martinanus/salt/documentacion/Informe de tesis/src/3 - Diseño e implementación/3.2.9 - Tarjeta SD.tex

\subsubsection{Zócalo para memoria SD}

Para incluir una memoria SD en el sistema, se utilizó un zócalo modelo DM3AT-SF-PEJM5 de Hirose Connector \cite{DM3AT-SF-PEJM5}. Este conector admite memorias micro SD y tiene un sistema de \textit{push-pull} que permite manipular más fácilmente la colocación de la memoria. Para la memoria micro SD se utilizó el modelo Micro SD Ultra 8GB Clase 10 de Sandisk \cite{sd_sandisk} porque se reutilizó de otro proyecto. Sin embargo, al ser un componente de simple extracción y reemplazo, se considera que se debe utilizar una unidad de almacenamiento de mayor memoria. \\

En la figura \ref{fig:sd_sch} se observa la conexión del circuito con el zócalo para micro SD. Se utilizó la interfaz SPI del MCU para la comunicación con la SD y se colocaron algunas resistencias de \textit{pull-up} recomendadas en los buses de datos o líneas desconectadas. También se incluyeron capacitores de desacople para reducir el ruido en la alimentación de la SD. El zócalo incluye además una conexión mecánica que permite determinar si existe una memoria colocada en el zócalo o no; esto se conecta con una entrada del MCU para poder considerar el estado físico real de la memoria. 

\begin{figure}[H]
    \centering
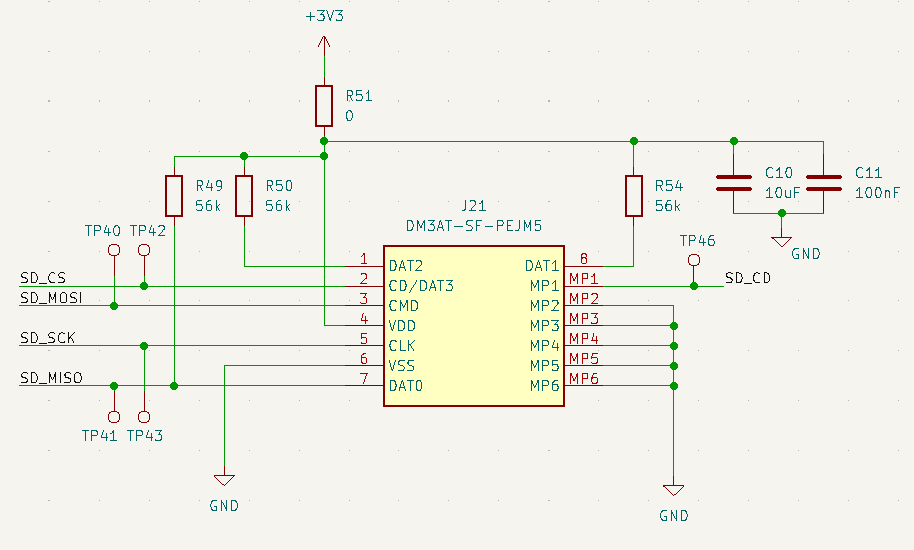
[picture p28: documentacion/Informe de tesis/src/img/sd_sch.png]
    
    \caption{Circuito de conexión del zócalo para memoria SD}
    \label{fig:sd_sch}
\end{figure}
