martinanus/salt/documentacion/Plan de Trabajo/src/7-Entregables.tex

\section{Entregables}

Se presenta a continuación una lista de los entregables del proyecto:

\begin{itemize}
    \item Documento de diseño de circuitos y selección de componentes
    \item Diseño de esquemático y layout de los PCB
    \item Desarrollo de firmware
    \item Prototipo funcional
    \item Documento de pruebas sobre el prototipo
    \item Informe integral del proyecto

    \end{itemize}
