martinanus/salt/documentacion/Informe de tesis/src/2 - Introducción específica/2.0 - intro.tex

En este capítulo se presentan los conceptos fundamentales necesarios para comprender el trabajo realizado, así como los módulos de hardware clave utilizados durante el desarrollo del sistema.
