martinanus/salt/documentacion/Informe de tesis/src/2 - Introducción específica/2.1 - intro.tex

\subsection{Módulos y componentes}

La figura \ref{fig:diagrama_bloques} muestra un diagrama en bloques del sistema, el cual proporciona una visión general que facilita la comprensión de los conceptos y módulos introducidos a lo largo de este capítulo.

\begin{figure}[H]
    \centering
    
    \caption{Diagrama en bloques del SAL/T}
    \label{fig:diagrama_bloques}
\end{figure}
