martinanus/salt/documentacion/Informe de tesis/src/1 - Introducción general/1.0 - intro.tex

En este capítulo se presenta el contexto, la motivación, los objetivos, el alcance y una descripción conceptual del proyecto. También se exponen sus requerimientos y una breve introducción a los sistemas críticos.
