martinanus/salt/documentacion/Informe de tesis/src/3 - Diseño e implementación/3.0 - intro.tex

En este capítulo se realiza una descripción general de la solución y se detalla el proceso de diseño e implementación del sistema a nivel hardware y firmware.
