martinanus/salt/documentacion/Informe de tesis/src/5 - Conclusiones/5.0 - intro.tex

En este capítulo se presentan las conclusiones generales obtenidas a partir de la realización del proyecto y los próximos pasos a seguir para la implementación del sistema en formaciones ferroviarias operativas.
