martinanus/salt/documentacion/Plan de Trabajo/src/8-DesgloseDeTareas.tex

\section{Desglose de Tareas}

Para realizar una mejor estimación de la duración del proyecto, es necesario descomponer el proyecto en tareas generales y estas en subtareas.  A continuación, se muestra un listado de todas las tareas necesarias para completar el proyecto con sus duraciones estimadas. 

\begin{enumerate}
    \item Estudio de Factibilidad   (60hs)
    \begin{enumerate}
        \item Lectura de documentos existentes sobre el SAL/T   (20hs)
        \item Lectura pliego de especificaciones técnicas SAL/T (5hs)
        \item Análisis y acuerdo de nuevas funcionalidad a implementar  (25hs)
        \item Entendimiento de código y puesta en marcha de primer prototipo SAL/T  (10hs)
    \end{enumerate}
    \item Diseño general de la solución (45hs)
    \begin{enumerate}
        \item Redacción de requerimientos del proyecto (7hs)
        \item Diseño de bloques de la solución (15hs)
        \item Análisis de comunicaciones entre módulos integrados (8hs)
        \item Análisis de disponibilidad de tiendas para componentes (10hs)
        \item Análisis de fabricantes de PCB (5hs)
    \end{enumerate}
    \item Desarrollo de hardware (255hs)
    \begin{enumerate}
        \item Investigación y selección de microcontrolador y kit de desarrollo (25hs)
        \item Investigación y selección de módulos GPS (10hs)
        \item Investigación y selección de módulos Wifi (10hs)
        \item Diseño de circuito de medición estado SIS (20hs)
        \item Diseño de circuitos RS485 (10hs)
        \item Diseño de panel frontal (15hs)
        \item Diseño circuitos de relé (15hs)
        \item Selección de componentes (40hs)
        \item Armado de esquemáticos (35hs)
        \item Asignación de pines microcontrolador (15hs)
        \item Selección de tecnología de PCB a utilizar (10hs)
        \item Diseño del PCB (50hs)
    \end{enumerate}
    \item Desarrollo de firmware (215hs)
    \begin{enumerate}
        \item Desarrollo conexión Wifi (15hs)
        \item Desarrollo de comunicación con protocolo MQTT (25hs)
        \item Desarrollo comunicación GPS (15hs)
        \item Desarrollo lecturas de velocidad (20hs)
        \item Desarrollo lectura de estados SIS (15hs)
        \item Desarrollo de lógica de perfiles intermitentes (15hs)
        \item Desarrollo de registro de datos local (25hs)
        \item Desarrollo de descarga de reporte de datos (25hs)
        \item Desarrollo de lógica general del sistema (30hs)
        \item Implementación de módulos en sistema operativo de tiempo real (30hs)
    \end{enumerate}
    \item Fabricación del prototipo (55hs)
    \begin{enumerate}
        \item Compra de componentes (10hs)
        \item Ensamblaje de componentes (15hs)
        \item Verificación de continuidad y señales en la placa (10hs)
        \item Pruebas sobre las comunicaciones (20hs)
    \end{enumerate}
    \item Verificación y validación (80hs)
    \begin{enumerate}
        \item Verificación de casos de uso del prototipo (35hs)
        \item Pruebas de integración (30hs)
        \item Validación de los requerimientos (20hs)
    \end{enumerate}
    \item Revisión de documentación (67hs)
    \begin{enumerate}
        \item Planificación del proyecto (15hs)
        \item Redacción del plan de trabajo (12hs)
        \item Documentación técnica del hardware (20hs)
        \item Documentación del código fuente (20hs)
        
    \end{enumerate}
    \item Presentación del proyecto (110hs)
    \begin{enumerate}
        \item Elaboración de diapositivas para la presentación (20hs)
        \item Confección del informe final (90hs)
    \end{enumerate}
\end{enumerate}

En total, se estiman 887 horas de trabajo necesarias para el desarrollo del proyecto. \\

Además, se presenta a modo de referencia, un cronograma con los plazos aproximados para completar cada una de las tareas generales. 

\begin{table}[h]
\begin{center}
\begin{tabular}{|l|l|l|l|l|l|l|l|l|l|l|l|l|}
\hline
\multicolumn{1}{|c|}{} & \multicolumn{12}{c|}{Meses} \\ \cline{2-13} 
\multicolumn{1}{|c|}
    {\multirow{-2}{*}{Tareas}} 
    & 1 & 2 & 3 & 4 & 5 & 6 & 7 & 8 & 9 & 10 & 11 & 12 \\ \hline
Estudio de Factibilidad             &
\cellcolor[HTML]{656565}{\color[HTML]{333333}}  &
                                                &
                                                &
                                                &
                                                &
                                                &
                                                &
                                                &
                                                &
                                                & 
                                                & \\ \hline
Diseño general de la solución                &
                                                &
\cellcolor[HTML]{656565}{\color[HTML]{333333}}  &                      
\cellcolor[HTML]{656565}{\color[HTML]{333333}}  &
                                                &
                                                &
                                                &
                                                &
                                                &
                                                &
                                                &
                                                & \\ \hline
Desarrollo de hardware      &
                                                &
                                                &    
\cellcolor[HTML]{656565}{\color[HTML]{333333}}  &
\cellcolor[HTML]{656565}{\color[HTML]{333333}}  &
\cellcolor[HTML]{656565}{\color[HTML]{333333}}  &
\cellcolor[HTML]{656565}{\color[HTML]{333333}}  &
                                                &
                                                &
                                                &
                                                &
                                                & \\ \hline
Desarrollo de firmware               &
                                                &
                                                &
                                                &
                                                &
                                                &
\cellcolor[HTML]{656565}{\color[HTML]{333333}}  &
\cellcolor[HTML]{656565}{\color[HTML]{333333}}  &
\cellcolor[HTML]{656565}{\color[HTML]{333333}}  &
                                                &
                                                &
                                                & \\ \hline
Fabricación del prototipo                                 &
                                                &
                                                &    
                                                &
                                                &
                                                &
                                                &
                                                &
                                                &
\cellcolor[HTML]{656565}{\color[HTML]{333333}}  &
                                                &
                                                & \\ \hline
Verificación y validación                &
                                                &
                                                &    
                                                &
                                                &
                                                &
                                                &
                                                &
                                                &   
\cellcolor[HTML]{656565}{\color[HTML]{333333}}  &
\cellcolor[HTML]{656565}{\color[HTML]{333333}}  &
                                                & \\ \hline
Revisión de documentación                &
                                                &                          
                                                &
                                                &
                                                &
                                                &
                                                &
                                                &
                                                &
                                                &            
\cellcolor[HTML]{656565}{\color[HTML]{333333}}  &
\cellcolor[HTML]{656565}{\color[HTML]{333333}}  & \\ \hline                                                
Presentación del proyecto                       &
                                                &
                                                &                          
                                                &
                                                &
                                                &
                                                &
                                                &
                                                &
                                                &
\cellcolor[HTML]{656565}{\color[HTML]{333333}}  &
\cellcolor[HTML]{656565}{\color[HTML]{333333}}  &
\cellcolor[HTML]{656565}{\color[HTML]{333333}}  \\ \hline
\end{tabular}
\end{center}
\end{table}
