martinanus/salt/documentacion/Informe de tesis/src/img/logo_fiuba_new.pdf

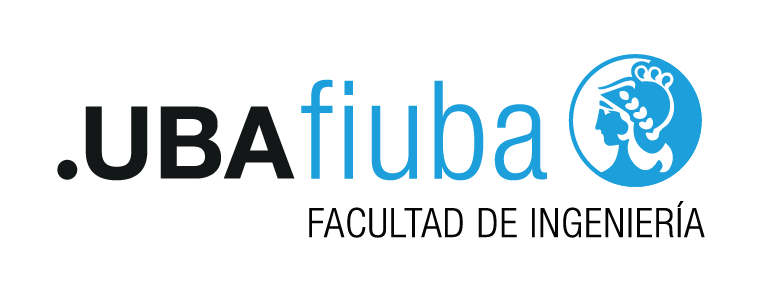
[picture p44: page 1]
