martinanus/salt/documentacion/Plan de Trabajo/Anus_SALT_Plan_de_trabajo.pdf

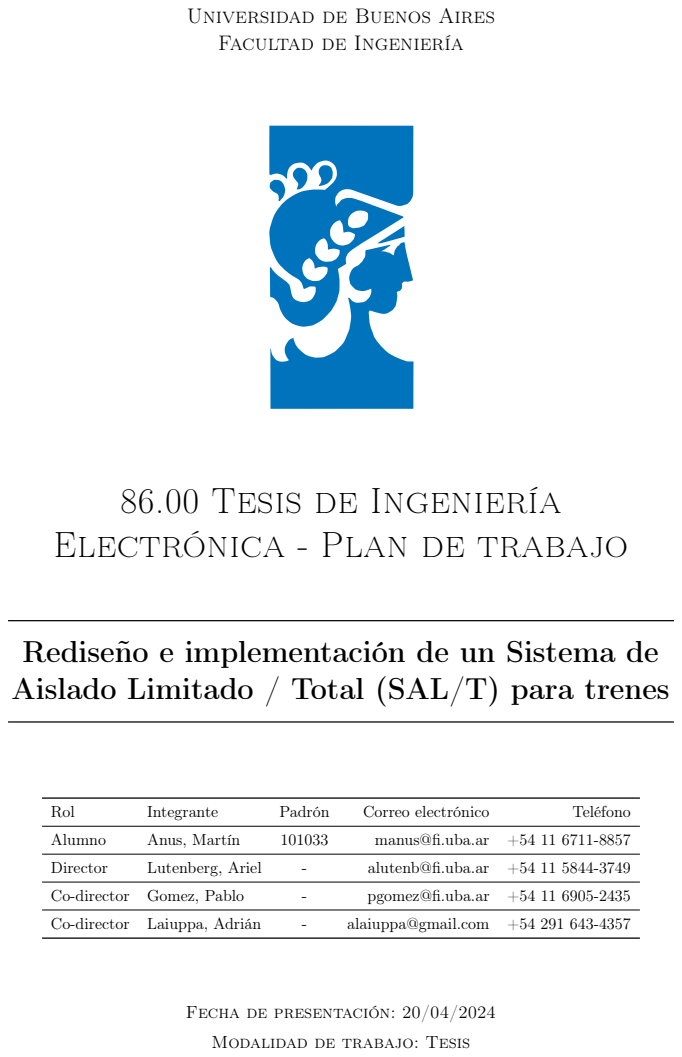
[picture p45: page 1]
Rol; Integrante; Padrón; Correo electrónico; Teléfono; Alumno; Anus, Martín; manus@fi.uba.ar +54 11 6711-8857; Director; Lutenberg, Ariel; alutenb@fi.uba.ar +54 11 5844-3749; Co-director Gomez, Pablo; pgomez@fi.uba.ar +54 11 6905-2435; Co-director Laiuppa, Adrián; alaiuppa@gmail.com +54 291 643-4357

Universidad de Buenos Aires

Facultad de Ingeniería

86.00 Tesis de Ingeniería

Electrónica - Plan de trabajo

Rediseño e implementación de un Sistema de
Aislado Limitado / Total (SAL/T) para trenes

Fecha de presentación: 20/04/2024

Modalidad de trabajo: Tesis

Sistema de Aislado Limitado / Total (SAL/T) | UBA - Facultad de Ingeniería

### Índice

1. Descripción | 1
2. Antecedentes | 2
3. Áreas profesionales de relevancia | 3
4. Objetivos | 4
5. Necesidad y soluciones existentes | 4
6. Alcance | 5
7. Entregables | 5
8. Desglose de Tareas | 6
9. Referencias | 8
10.Anexo | 9

### 1. Descripción

Las formaciones ferroviarias cuentan con varios Sistemas Instrumentados de Seguridad (SIS) a bordo con el objetivo de supervisar el correcto funcionamiento de los subsistemas críticos como por ejemplo, la protección de coche a la deriva, el sistema de hombre vivo o la seguridad de puertas.

Estos sistemas están diseñados para que, ante la detección de una falla crítica, se produzca la detención de la formación de manera inmediata. Esto se logra controlando las señales de Corte de Tracción (CT) y de Freno de Emergencia (FE). En esta situación, la formación puede ser remolcada o bien, desactivar todos los SIS bajo estricta supervisión y continuar andando con el control manual del conductor hasta una estación cercana para descender a los pasajeros y luego a un taller para ser reparada.

El Sistema de Aislamiento Limitado/Total, por sus siglas SAL/T, es un equipo que permite una circulación controlada y más segura de la formación cuando uno de los SIS se encuentra en falla. Al activar el Modo Aislado Limitado (MAL), el SAL/T va a deshabilitar solamente el SIS que está en fallo y controlar las señales de CT y FE para poder continuar con la circulación de la formación. Para hacerlo de manera segura, el SAL/T va a contar con múltiples fuentes de medición de la velocidad de la formación y va a activar las señales de CT y FE para frenarla en caso de que se excedan los límites estipulados. En el Modo Aislado Total (MAT), se libera la velocidad de precaución y puede ser solamente aplicado por personal superior en el caso que la formación se encuentre sin pasajeros y muy alejada del centro reparador. Ambas activaciones deben ser registradas dentro del equipo así como también cualquier falla detectada, cambio de configuración en las velocidades permitidas o cualquier evento significativo para la seguridad de la formación.

Además, el SAL/T cuenta con otras funcionalidad como la comunicación con el conductor a través de una interfaz donde se muestra el estado de los SIS, la velocidad medida en todo momento y un indicador de la zona donde se encuentra la formación. En caso de no contar con una medición de velocidad válida y activar el MAL, el SAL/T entra en Modo Intermitente (MI) y controla la formación activando y desactivando la tracción y el freno acorde a los perfiles de tiempos preconfigurados según las características de la formación para no exceder ciertas velocidades de precaución. Desde el panel formal, el conductor puede seleccionar distintos perfiles intermitentes. También, el SAL/T tiene la posibilidad de conectarse con una central operativa para informar su estado y recibir remotamente instrucciones.

Este equipo es considerado un sistema crítico ya que, en caso de fallar, puede conllevar pérdidas de vidas humanas o daños importantes tanto de propiedades como del entorno.

En el 2019, el Ingeniero Iván Di Vito presentó un prototipo de este sistema con pruebas de campo en los talleres de Trenes Argentinos siguiendo las fases y recomendaciones de la norma UNE-EN 50126 [1]; “Aplicaciones ferroviarias. Especificación y demostración de la fiabilidad, la disponibilidad, la mantenibilidad y la seguridad (RAMS)”. En el año 2022, los ingenieros Fernando Iglesias y Matías Sambrizzi realizaron el trabajo “Central Operativa para el SAL/T” donde se desarrolló la central operativa para monitorear, controlar y configurar múltiples formaciones equipadas con el SAL/T de manera remota desde un centro de operaciones. Ambos trabajos fueron desarrollados con el acompañamiento del Grupo de Investigación en Calidad y Seguridad de las Aplicaciones Ferroviarias (GICSAFe) como trabajo final de grado de Ingeniería Electrónica en la Universidad de Buenos Aires teniendo como directores al Dr. Ing. Ariel Lutenberg y al Dr. Ing. Pablo Gomez.

En este trabajo, se busca hacer un rediseño del prototipo del SAL/T implementando algunas mejoras sugeridas por Trenes Argentinos en el pliego de especificaciones técnicas ET.SO.No 046/18–E3 del 2022, utilizando un microcontrolador y componentes más modernos y un firmware basado en un sistema operativo de tiempo real que resulte más portable que el actual. A continuación se muestra un diagrama en bloques del sistema a desarrollar:


Figura 1: Diagrama en bloques del SAL/T

También se muestra la interfaz humano-máquina (IHM) diseñada para comunicarse con el conductor de la formación:

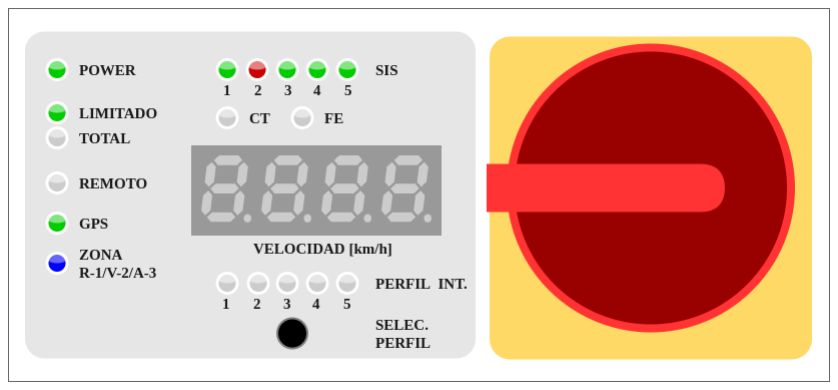
[picture p46: figure]

Figura 2: Interfaz humano-máquina del SAL/T

### 2. Antecedentes

El Grupo de Investigación en Calidad y Seguridad de las Aplicaciones Ferroviarias (GICSA-Fe) fue creado en 2017 en el marco del Consejo Nacional de Investigaciones Científicas y Técnicas (CONICET) de la República Argentina [2]. En el grupo participan investigadores, docentes y alumnos de diferentes instituciones públicas argentinas quienes realizan desarrollos de sistemas electrónicos e informáticas para aplicaciones ferroviarias relacionadas con la seguridad. Muchos de los prototipos desarrollados son instalados y entregados junto a toda la documentación, respetando normas internacionales de seguridad, para luego transferir el derecho de uso, fabricación y mantenimiento a los clientes.

La empresa estatal Trenes Argentinos Operaciones [3] encargó al grupo CONICET-GICSAFe el desarrollo de un prototipo del SAL/T en el año 2017. El ingeniero Iván Di Vito, en ese momento estudiante de la carrera de Ingeniería Electrónica en la UBA y allegado al grupo de investigación tomó el proyecto que finalizaría en el año 2019 con la entrega de un prototipo funcional del SAL/T luego de varias pruebas de campo en los talleres de Trenes Argentinos junto a toda la documentación requeridas por las normas de seguridad ferroviarias para este tipo de desarrollos [4]. El trabajo realizado incluyó el relevamiento de los requerimientos del proyecto, el desarrollo conceptual de la solución propuesta, el diseño e implementación del hardware y firmware, la puesta en marcha y realización de pruebas de campo de un prototipo funcional. El mismo se realizó de acuerdo a la norma UNE-EN 50126, aplicando técnicas de patrones de diseño de hardware y software [5]. Este trabajo fue publicado por el Congreso Argentino de Sistemas Embebidos (CASE) en el año 2019 en la categoría de artículo [6].

En el año 2021, otros dos estudiantes de la carrera de Ingeniería Electrónica de la UBA, Fernando Iglesias y Matias Sambrizzi, emprendieron un proyecto para el desarrollo de la central operativa del SAL/T en el mismo contexto de acuerdo entre Trenes y CONICET-GICSAFe. El objetivo de dicho proyecto fue desarrollar el software de una central operativa que permita administrar y configurar de forma remota dispositivos de supervisión de seguridad de formaciones ferroviarias SAL/T [7]. Para esto, se implementó un servicio de monitoreo y control que permite visualizar en tiempo real los datos recibidas y enviar comando de control a los dispositivos activos, la gestión de configuración de dispositivos, la base de datos, los componentes de seguridad necesarios para las comunicaciones e información almacenada y la gestión de usuarios y perfiles.

### 3. Áreas profesionales de relevancia

Esta Tesis está enmarcada principalmente dentro del área de Sistemas Digitales y Computación, según lo especificado en la versión 2009, Modificación 2018, del plan de estudios de la Carrera de Ingeniería Electrónica de la Facultad de Ingeniería de la Universidad de Buenos Aires [8].

En particular, están vinculadas a este proyecto las siguientes actividades reservadas al tıitulo de Ingeniero Electrónico:

- Diseñar, proyectar y calcular hardware y software de sistemas embebidos y dispositivos lógicos programables
- Proyectar, dirigir y controlar la construcción, implementación, mantenimiento y operación de lo mencionado anteriormente.

De la misma forma, son particularmente relevantes al proyecto los siguientes alcances del titulo de Ingeniero Electrónico:

- Estudio, planificación, proyectos, estudios de factibilidad técnico-económicos, programación, dirección, construcción, instalación, puesta en marcha, operación, ensayo, mediciones, mantenimiento, reparación, modificación, transformación e inspección de:

- Sistemas, subsistemas, equipos, componentes, partes, piezas (Hardware), de procesamiento electrónico de datos en todas sus aplicaciones incluyendo su programación (Software) asociada.
- Sistemas, subsistemas, equipos, componentes, partes, piezas que impliquen electrónica, de navegación o señalización o cualquier otra aplicación al movimiento de vehículos terrestres, aéreos, marítimos o de cualquier otro tipo.

### 4. Objetivos

### 4.1. Objetivos generales

Se busca diseñar una solución para aumentar la seguridad en las formaciones ferroviarias ante fallas en los Sistemas Instrumentados de Seguridad mediante un mejor control y monitoreo de velocidad de la formación en tiempo real. La solución debe ser compatible con los mecanismos de seguridad y sistemas instalados actualmente en las formaciones de Trenes Argentinos.

### 4.2. Objetivos particulares

- Rediseñar el sistema SAL/T a partir de los trabajos existentes y el pliego de especificaciones técnicas propuestos por Trenes Argentinos
- Rediseñar el hardware del SAL/T utilizando componentes vigentes en el mercado
- Generar un firmware portable basado en un sistema operativo de tiempo real
- Construir un prototipo del proyecto y realizar pruebas de funcionamiento en un entorno similar al real
- Favorecer el desarrollo de tecnología nacional

### 5. Necesidad y soluciones existentes

La empresa de Trenes Argentinos mencionó en reiteradas oportunidades la disconformidad con la situación actual de las formaciones ferroviarias frente a algún fallo en los Sistemas Instrumentados de Seguridad (SIS) ya que, al entrar alguno de ellos en fallo, obliga a la formación a ser remolcada o, lo que sucede más frecuentemente en la práctica, a continuar hasta la próxima estación para descender a los pasajeros deshabilitando todos los SIS con los que cuenta la formación. Esto presenta una situación de riesgo ya que la formación pasa a depender fuertemente de la manualidad del conductor sin ningún sistema de seguridad monitoreando y asistiendo la conducción.

Al mismo tiempo, la empresa no encuentra alternativas comerciales para satisfacer las necesidades de un Sistema de Aislamiento Limitado / Total ya que necesita integrar distintos SIS y fuentes de medición que no son necesariamente del mismo fabricante o con especificaciones genéricas que permitan su fácil integración.

Por estos motivos, Trenes Argentinos solicitó al grupo CONICET-GICSAFe que diseñara un SAL/T a medida para cumplir con los requerimientos específicos de sus formaciones. En 2019 se entregó una primera versión del prototipo que permitía satisfacer las funciones más importantes del sistema. Sin embargo, antes de requerir una versión productiva y fabricable en cantidades, se determinó que faltaban implementar algunas funcionalidades adicionales para que se pueda instalar un SAL/T en las formaciones. El pliego de especificaciones técnicas para la versión completa del SAL/T se encuentra en disponible en [9].

Los cambios más relevantes mencionados en el documento que dan lugar a rediseñar el prototipo antes de producirlo en masa son:

- Utilización de un microcontrolador de mayor capacidad y más vigente
- Generación de un firmware más portable basado en un sistema operativo de tiempo real
- Aislamiento del SIS en falla particular en Modo Aislado Limitado sin interrumpir el funcionamiento del resto de los SIS
- Selección de distintos perfiles intermitentes desde el panel frontal del SAL/T
- Conector de zona para poder determinas distintas zonas de tránsito para la formación y activar cambios en otros sistemas de la formación
- Registro interno de eventos para cambios de estado de SIS, activación de modos, excesos de velocidad y activación de señales de Corte de Tracción y Freno de Emergencia

### 6. Alcance

El proyecto consiste en diseñar, desarrollar e implementar un nuevo protitpo del SAL/T teniendo en cuenta que se deben agregar nuevas funcionalidades requeridas, que el hardware debe ser actualizado con componentes vigentes y disponibles actualmente en el mercado internacional y que el firmware desarrollado debe estar basado en un sistema operativo de tiempo real que resulte portable.

Para establecer los requerimientos del proyecto, se contempló el prototipo preexistente del SAL/T y el pliego de especificaciones técnicas que generó Trenes Argentinos teniendo en consideración las limitaciones de tiempos y presupuesto que hace sentido para un proyecto de fin de carrera de grado. En el Anexo, se adjunta un listado con el detalle de los requerimientos considerados para este proyecto.

Una vez finalizado el diseño del sistema, el prototipo debe ser fabricado sobre una placa PCB y se deben montar todos los componentes para su correcto funcionamiento. Se deberán realizar pruebas de laboratorio en las condiciones de funcionamiento para verificar que se cumplas todos los requerimientos establecidos. De ser posible, se intentará coordinar con Trenes Argentinos para realizar algunas pruebas de campo en los talleres de la empresa.

### 7. Entregables

Se presenta a continuación una lista de los entregables del proyecto:

- Documento de diseño de circuitos y selección de componentes
- Diseño de esquemático y layout de los PCB
- Desarrollo de firmware
- Prototipo funcional
- Documento de pruebas sobre el prototipo
- Informe integral del proyecto

### 8. Desglose de Tareas

Para realizar una mejor estimación de la duración del proyecto, es necesario descomponer el proyecto en tareas generales y estas en subtareas. A continuación, se muestra un listado de todas las tareas necesarias para completar el proyecto con sus duraciones estimadas.

1. Estudio de Factibilidad (60hs)

1.1 Lectura de documentos existentes sobre el SAL/T (20hs)
1.2 Lectura pliego de especificaciones técnicas SAL/T (5hs)
1.3 Análisis y acuerdo de nuevas funcionalidad a implementar (25hs)
1.4 Entendimiento de código y puesta en marcha de primer prototipo SAL/T (10hs)
2. Diseño general de la solución (45hs)

2.1 Redacción de requerimientos del proyecto (7hs)
2.2 Diseño de bloques de la solución (15hs)
2.3 Análisis de comunicaciones entre módulos integrados (8hs) 2.4 Análisis de disponibilidad de tiendas para componentes (10hs) 2.5 Análisis de fabricantes de PCB (5hs)
3. Desarrollo de hardware (255hs)

3.1 Investigación y selección de microcontrolador y kit de desarrollo (25hs) 3.2 Investigación y selección de módulos GPS (10hs)
3.3 Investigación y selección de módulos Wifi (10hs)
3.4 Diseño de circuito de medición estado SIS (20hs) 3.5 Diseño de circuitos RS485 (10hs)
3.6 Diseño de panel frontal (15hs)
3.7 Diseño circuitos de relé (15hs) 3.8 Selección de componentes (40hs)
3.9 Armado de esquemáticos (35hs)
3.10 Asignación de pines microcontrolador (15hs) 3.11 Selección de tecnología de PCB a utilizar (10hs) 3.12 Diseño del PCB (50hs)
4. Desarrollo de firmware (215hs)

4.1 Desarrollo conexión Wifi (15hs)
4.2 Desarrollo de comunicación con protocolo MQTT (25hs) 4.3 Desarrollo comunicación GPS (15hs)
4.4 Desarrollo lecturas de velocidad (20hs)
4.5 Desarrollo lectura de estados SIS (15hs)
4.6 Desarrollo de lógica de perfiles intermitentes (15hs) 4.7 Desarrollo de registro de datos local (25hs)
4.8 Desarrollo de descarga de reporte de datos (25hs)
4.9 Desarrollo de lógica general del sistema (30hs)
4.10 Implementación de módulos en sistema operativo de tiempo real (30hs)

5. Fabricación del prototipo (55hs)

5.1 Compra de componentes (10hs)

5.2 Ensamblaje de componentes (15hs)

5.3 Verificación de continuidad y señales en la placa (10hs)

5.4 Pruebas sobre las comunicaciones (20hs)

6. Verificación y validación (80hs)

6.1 Verificación de casos de uso del prototipo (35hs)

6.2 Pruebas de integración (30hs)

6.3 Validación de los requerimientos (20hs)

7. Revisión de documentación (67hs)

7.1 Planificación del proyecto (15hs)

7.2 Redacción del plan de trabajo (12hs)

7.3 Documentación técnica del hardware (20hs)

7.4 Documentación del código fuente (20hs)

8. Presentación del proyecto (110hs)

8.1 Elaboración de diapositivas para la presentación (20hs)

8.2 Confección del informe final (90hs)

En total, se estiman 887 horas de trabajo necesarias para el desarrollo del proyecto.

Además, se presenta a modo de referencia, un cronograma con los plazos aproximados para completar cada una de las tareas generales.

Meses Tareas | 1 | 2 | 3 | 4 | 5 | 6 | 7 | 8 | 9 | 10 | 11 | 12

Estudio de Factibilidad
Diseño general de la solución Desarrollo de hardware
Desarrollo de firmware
Fabricación del prototipo
Verificación y validación
Revisión de documentación
Presentación del proyecto

### 9. Referencias

### Referencias

[1] UNE-EN 50126-1. Aplicaciones ferroviarias. Especificación y demostración de la fiabilidad, la disponibilidad, la mantenibilidad y la seguridad (RAMS). 2005. https://www.une.org/encuentra-tu-norma/busca-tu-norma/norma?c=N0033106
[2] GICSAFe Grupo de Investigación en Calidad y Seguridad de las Aplicaciones Ferroviarias. https://sites.google.com/view/conicet-gicsafe.
[3] Trenes | Argentinos | Trenes | Argentinos | Operaciones, | empresa | del | estado.
https://www.argentina.gob.ar/transporte/trenes-argentinos.
[4] Di Vito, Iván Mariano, “Aplicación de la técnica de patrones de diseño a la implementación de un Sistema de Aislamiento Limitado/Total ferroviario,” 2019 https://bibliotecadigital.fi.uba.ar/items/show/18446 .
[5] Ashraf Armoush. “Design Patterns for Safety-Critical Embedded Systems” RWTH Aachen University. 2010.
[6] Ivan | Mariano | Di | Vito, | Pablo | Gomez, | Ariel | Lutenberg,
Adrian | Laiuppa | “Sistema | de | supervisión | de | la | seguridad
del | material | ferroviario | utilizando | patrones | de | diseño”. | 2019.
https://drive.google.com/file/d/1FDtRL4We4daZ7XrJ81sL2f6HrZbYlOuG/view.
[7] Iglesias Fernando Julio, Sambrizzi Matias, “Central Operativa para el Sistema de Aislamiento Limitado/Total Ferroviario (SAL/T)“ . Plan de trabajo, 2022.
[8] Plan | de | estudios | de | Ingeniería | Electrónica | - | Facultad | de | Inge-
niería, | Universidad | de | Buenos | Aires. | Plan | 2009, | modificación | 2018.
https://cms.fi.uba.ar/uploads/ELECTRONICA_Modificacion_2018_Plan_2009_Ingenieria_Electronica_RCS_1801_18_f22d3d7a5a.pdf (https://cms.fi.uba.ar/uploads/ELECTRONICA_Modificacion_2018_Plan_2009_Ingenieria_Electronica_RCS_1801_18_f22d3d7a5a.pdf) .
[9] SISTEMA DE AISLADO LIMITADO / TOTAL (SAL-T). ESPECIFICACIÓN TÉCNICA. Bypass Sistemas Instrumentados de Seguridad a Bordo del Material Rodante ET.SO. No 046 /18 – E3. 2022.

### 10. Anexo

### 10.1. Detalle de requerimientos

1. Grupo de requerimientos asociados con la interfaz humano-máquina

1.1 La interfaz debe contar con una llave rotativa para activar el modo aislado limitado. 1.2 La interfaz debe mostrar la velocidad media del equipo en km/h con 4 dígitos.

1.3 La interfaz debe indicar el estado de la señal de corte de tracción.

1.4 La interfaz debe indicar el estado de la señal de freno de emergencia.

1.5 La interfaz debe indicar la presencia de un comando remoto de la central operativa.

1.6 La interfaz debe indicar el estado del módulo GPS.

1.7 La interfaz debe indicar el estado de la alimentación.

1.8 La interfaz debe indicar el modo en el que se encuentra el sistema.

1.9 La interfaz debe contener un control local por fuera del panel frontal para activar el modo aislado total.

1.10 La interfaz debe indicar con un LED RGB en cuál de las 3 zonas geográficas predefinidas se encuentra el material rodante.

1.11 La interfaz debe indicar el estado de los distintas Sistemas Instrumentados de Seguridad conectados al SAL/T con un LED RGB para cada SIS.

1.12 La interfaz debe contar con una botonera o switch que permita cambiar el perfil para modo de tracción intermitente.

1.13 La interfaz debe indicar el perfil seleccionado para modo de tracción intermitente.

1.14 La interfaz debe contener un buzzer interno para indicaciones sonoras.

2. Grupo de requerimientos asociados a la comunicación con el registrador de eventos

2.1 El sistema debe informar al registrador de eventos la activación del modo aislado limitado.

2.2 El sistema debe informar al registrador de eventos si la alimentación es correcta.

2.3 El sistema debe informar al registrador de eventos la activación del freno de emergencia.

2.4 El sistema debe informar al registrador de eventos la activación del corte de tracción.

3. Grupo de requerimientos asociados al registro de datos

3.1 El sistema debe mantener un registro de datos local donde se registran los siguientes eventos con marca de tiempo:
- Activación/Desactivación del modo aislado limitado
- Activación/Desactivación del modo aislado total (local o remota)
- Referencia de velocidad adoptada y sus permutaciones
- Cobertura de señal GPS
- Ciclos de permiso, corte y freno en modo de tracción intermitente
- SIS en fallo
- Velocidad desarrollada
- Zona de circulación

3.2 El sistema debe permitir descargar los datos registrados mediante una interfaz serie

3.3 El sistema debe poder descargar los datos registrados de manera remota

4. Grupo de requerimientos asociados a la comunicación con la central operativa

4.1 El sistema debe informar periódicamente (con un tiempo configurable) su estado a la central operativa a través de la red de datos WiFi.
4.2 Debe existir la posibilidad de usar 2 proveedores distintos de datos de manera simultánea.
4.3 Debe existir la posibilidad de conectarse alternadamente a más de una red Wifi
4.4 El protocolo de comunicación con la central operativa debe ser MQTT.
4.5 El sistema debe ser capaz de recibir un comando remoto que anule el corte de tracción y el freno de emergencia bajo cualquier condición (modo aislado total).

4.6 El sistema debe ser capaz de recibir un comando remoto que active el corte de tracción y el freno de emergencia bajo cualquier condición (modo parada total).

4.7 El sistema debe ser capaz de recibir un comando remoto que active el corte de tracción y anule el freno de emergencia bajo cualquier condición (modo coche en deriva).

4.8 El sistema debe ser capaz de recibir un comando remoto que active el corte de tracción y el freno de emergencia de forma intermitente en ciclos de tiempo configurables (modo intermitente).

4.9 El sistema debe ser capaz de recibir un comando remoto que cancele cualquier comando remoto vigente.
4.10 El sistema debe ser capaz de recibir comandos remotos que modifiquen sus parámetros internos configurables.
4.11 Si no se recibe un nuevo comando remoto luego de un tiempo configurable (por defecto 10 segundos, máximo 1 minuto), debe volver al algoritmo de activación de corte de tracción y freno de emergencia por defecto.
4.12 Ante un comando remoto recibido, debe enviar una confirmación de recepción que permita a la central operativa decidir si es necesaria o no una retransmisión.
4.13 Debe utilizar algún mecanismo de encriptación para el enlace con la central operativa.
5. Grupo de requerimientos asociados al modo normal de funcionamiento

5.1 El modo normal el sistema no debe intervenir en el funcionamiento del material rodante (prioridad alta).

5.2 El sistema debe obtener en todo momento la mejor estimación posible de la velocidad de la formación.
5.3 Debe ser capaz de recibir la velocidad a partir de una señal digital provista por el registrador de eventos Hasler Teloc 1500
5.4 Debe ser capaz de calcular la velocidad a partir de un sistema GPS integrado.
5.5 Debe ser capaz de calcular la velocidad a partir de un generador de impulsos
5.6 El rango de velocidad soportado por el sistema tiene que estar entre 0 y 120 km/h.

5.7 La estimación de velocidad debe tener una precisión del 2
5.8 El sistema debe determinar la posición del material rodante para activar un contacto seco de relé según la zona de operación donde se encuentre.
6. Grupo de requerimientos asociados al modo aislado limitado

6.1 En modo aislado limitado el sistema debe evitar la aplicación del corte de tracción. 6.2 En modo aislado limitado el sistema debe evitar la aplicación del freno de emergencia. 6.3 Ante cualquier error interno, el sistema debe dejar de intervenir en la aplicación del corte de tracción.

6.4 Ante cualquier error interno, el sistema debe dejar de intervenir en la aplicación del freno de emergencia.

6.5 En modo aislado limitado el sistema debe emitir una señal sonora intermitente a través de un buzzer.

6.6 En modo aislado limitado el sistema debe evitar que la velocidad del material rodante supere una serie de límites configurados.

6.6.1 Si al pasar de modo normal a modo aislado limitado no se cuenta con una estimación de velocidad, debe activar el corte de tracción y el freno de emergencia por 30 segundos.
6.6.2 Si se supera una velocidad configurable (por defecto 30 km/h), debe activar el corte de tracción y emitir una señal sonora continua a través de un buzzer. 6.6.3 Si se supera una velocidad configurable (por defecto 36 km/h), debe activar el freno de emergencia.
6.6.4 na vez aplicado, el corte de tracción debe dejar de aplicarse si la velocidad vuelve a ser menor a una velocidad configurable (por defecto 25 km/h).
6.6.5 Una vez aplicado, el freno de emergencia sólo debe dejar de aplicarse luego de un tiempo configurable (por defecto 30 segundos) desde que se superó el límite. 6.6.6 Si la lectura de velocidad es inválida, debe activar y desactivar el corte de tracción y freno de emergencia de manera alternada en ciclos de tiempo según perfiles preconfigurados (modo de tracción intermitente).

6.7 El sistema debe interactuar con 5 Sistemas Instrumentados de Seguridad.

6.8 El sistema debe ser capaz de identificar qué SIS está fallando y aislar solamente este dejando los demás SIS operativos.

6.9 El sistema debe medir la posición del material rodante para modificar las velocidades máximas según la zona de operación donde se encuentre.

7. Grupo de requerimientos asociados al modo aislado total

7.1 El sistema solo puede acceder a este modo accionando el control local o mediante comando remoto.

7.2 En el modo aislado total el sistema debe liberar la velocidad de circulación.

7.3 El sistema debe registrar en el registro de datos la activación de este modo.

8. Grupo de requerimientos asociados al modo de tracción intermitente

8.1 El sistema solo deberá acceder a este modo cuando se encuentre en modo aislado limitado y no cuente con ninguna medición de velocidad válida.

8.2 El sistema debe permitir la configuración remota de distintos perfiles de operación de manera remota en donde se configuran los valores de Tiempo del permiso de Tracción, Tiempo de ciclo en deriva, Cantidad de ciclos antes de aplicar freno y Tiempo de espera antes de comienzo de nuevo ciclo.

9. Grupo de requerimientos asociados al hardware y al gabinete

9.1 El sistema utilizará una fuente externa de 5 V de tensión continua que pueda soportar hasta 25W de potencia.

9.2 Los conectores deben estar bien identificados para facilitar la correcta conexión

9.3 El sistema debe poseer una placa de circuito impreso con el procesador y periféricos necesarios para el procesamiento de las señales del material rodante y una segunda placa para el los elementos necesarios para la interacción con el conductor

9.4 El diseño de la placa de circuito impreso debe contemplar las recomendaciones de la norma IPC 2221 a fines de asegurar la manufacturabilidad del equipo.

10. Grupo de requerimientos asociados al desarrollo del firmware

10.1 El desarrollo del software debe contemplar las recomendaciones de las normas UNE-EN 50126 y UNE-EN 50128.

10.2 El sistema debe trabajar con un sistema operativo en tiempo real para mejorar el desempeño y la seguridad del equipo.
