martinanus/salt/documentacion/Informe de tesis/src/img/pcb_3d_no_comps.png

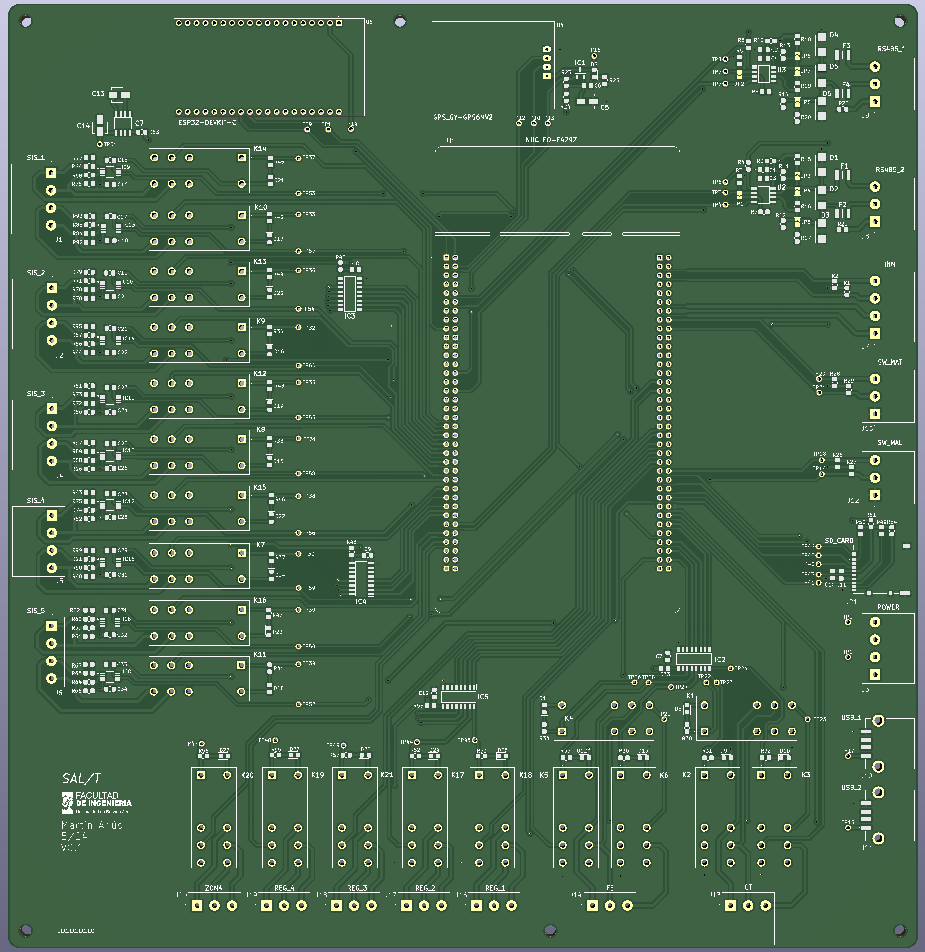
documentacion/Informe de tesis/src/img/pcb_3d_no_comps.png
