martinanus/salt/hardware/salt/temp_files/1.png

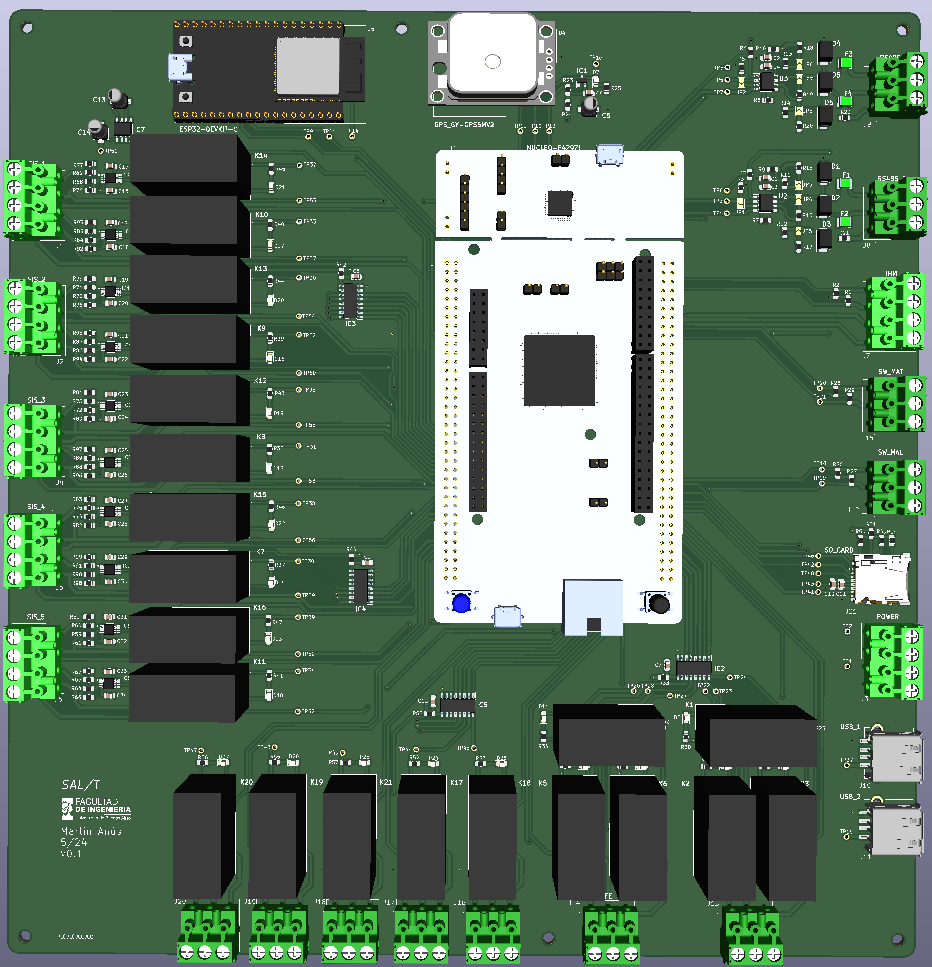
hardware/salt/temp_files/1.png
