martinanus/salt/hardware/salt/temp_files/3.png

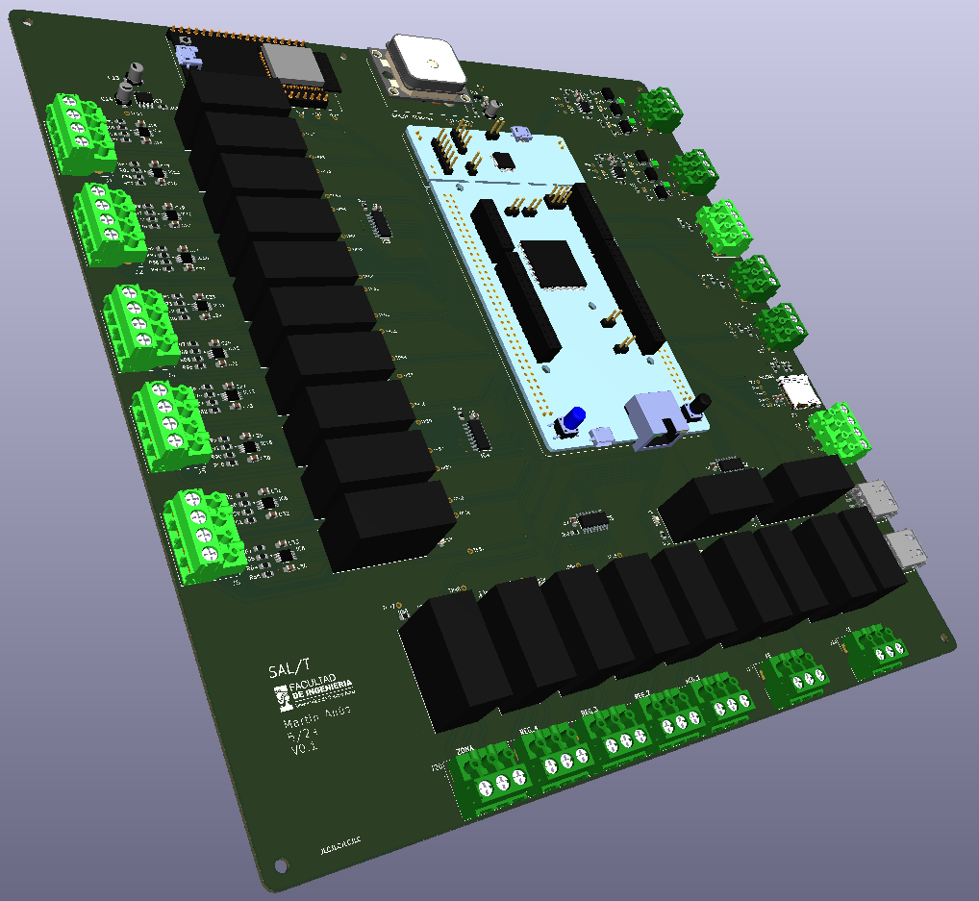
hardware/salt/temp_files/3.png
