martinanus/salt/hardware/salt/temp_files/4.png

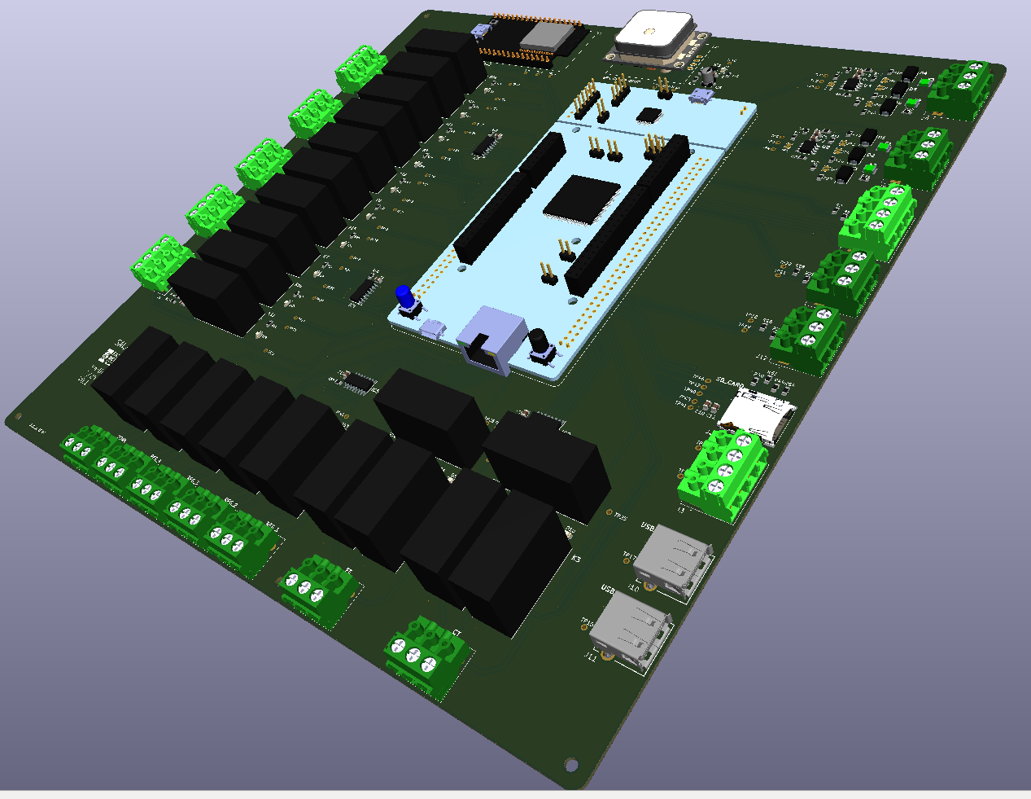
hardware/salt/temp_files/4.png
