martinanus/salt/hardware/salt/temp_files/5.png

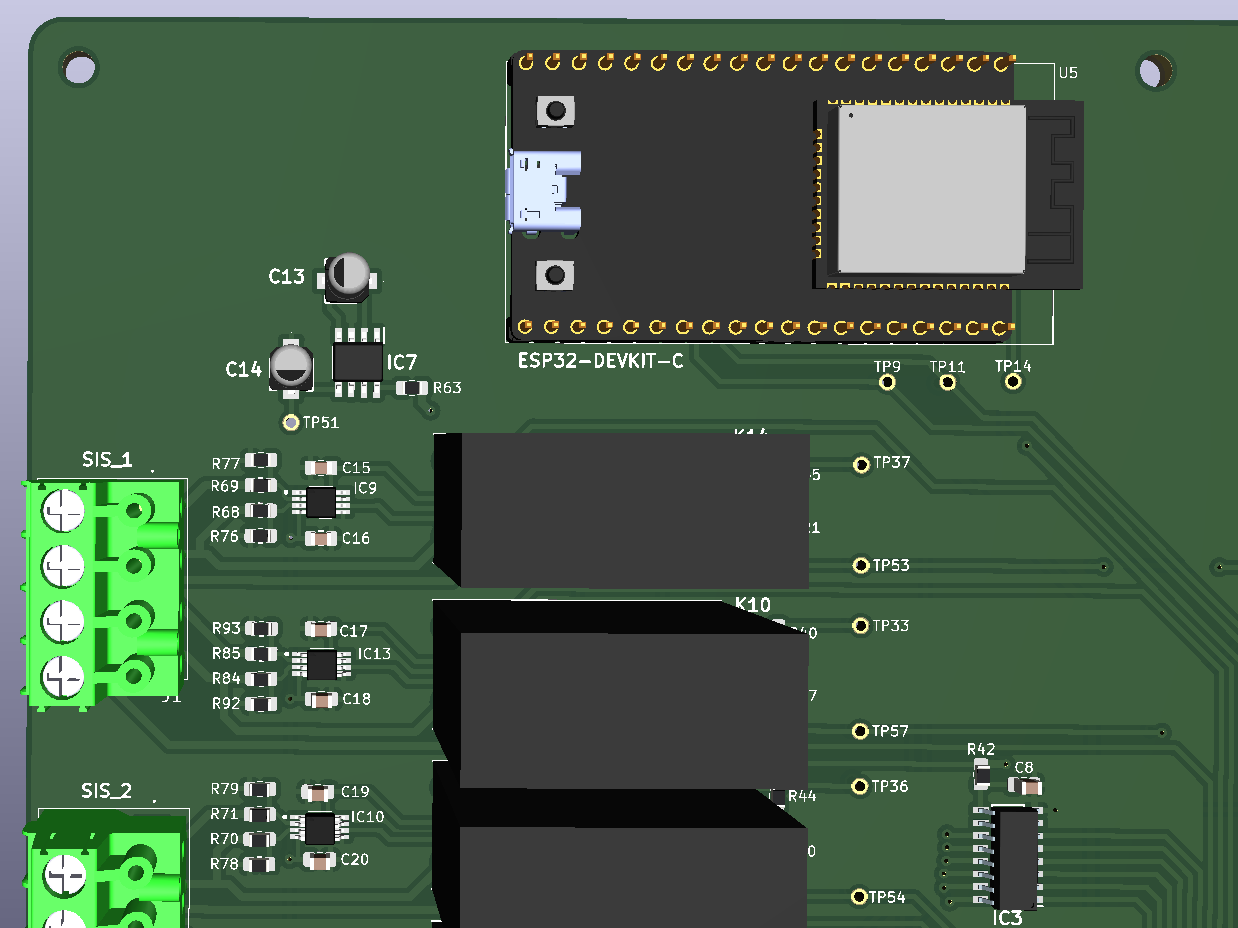
hardware/salt/temp_files/5.png
