martinanus/salt/hardware/salt/temp_files/6.png

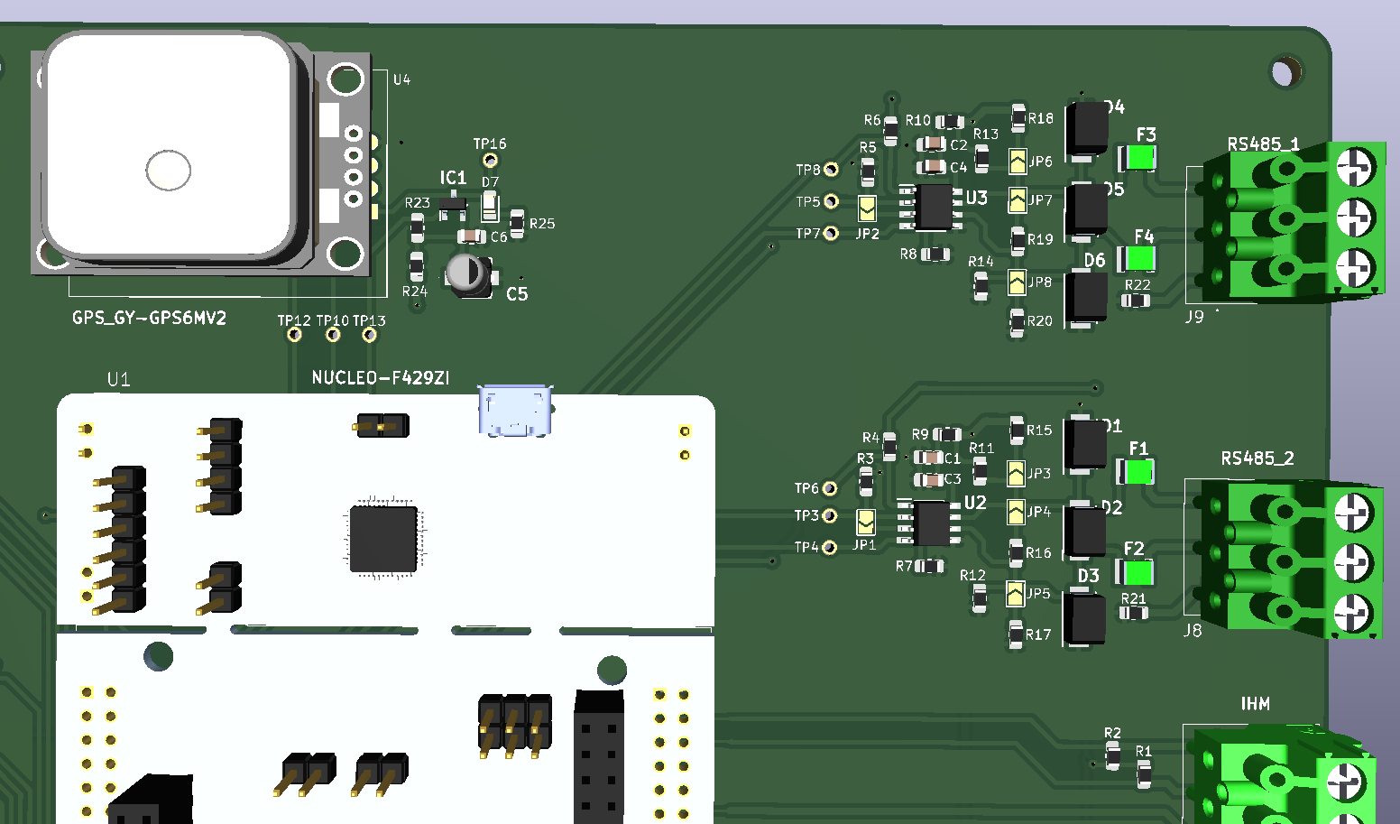
hardware/salt/temp_files/6.png
