martinanus/salt/hardware/salt/temp_files/7.png

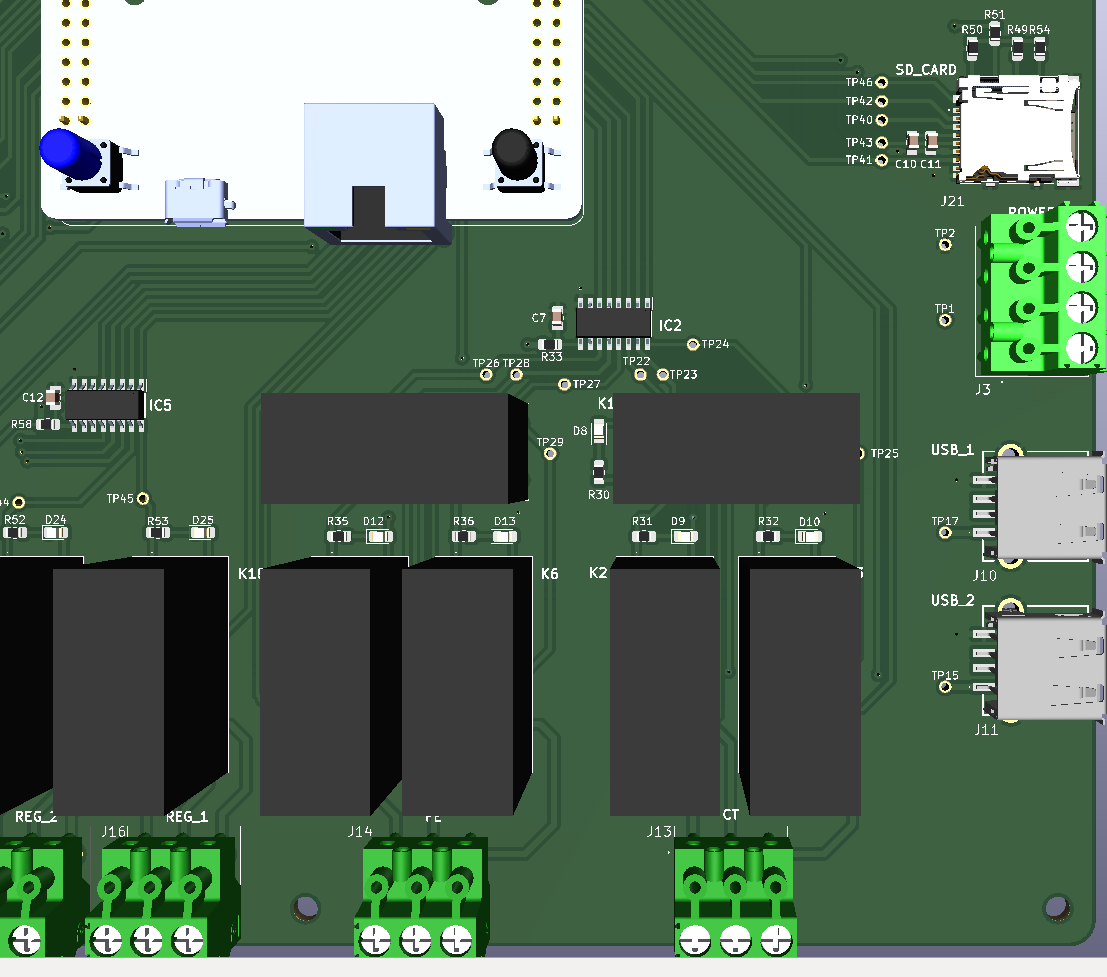
hardware/salt/temp_files/7.png
