martinanus/salt/hardware/salt/temp_files/8.png

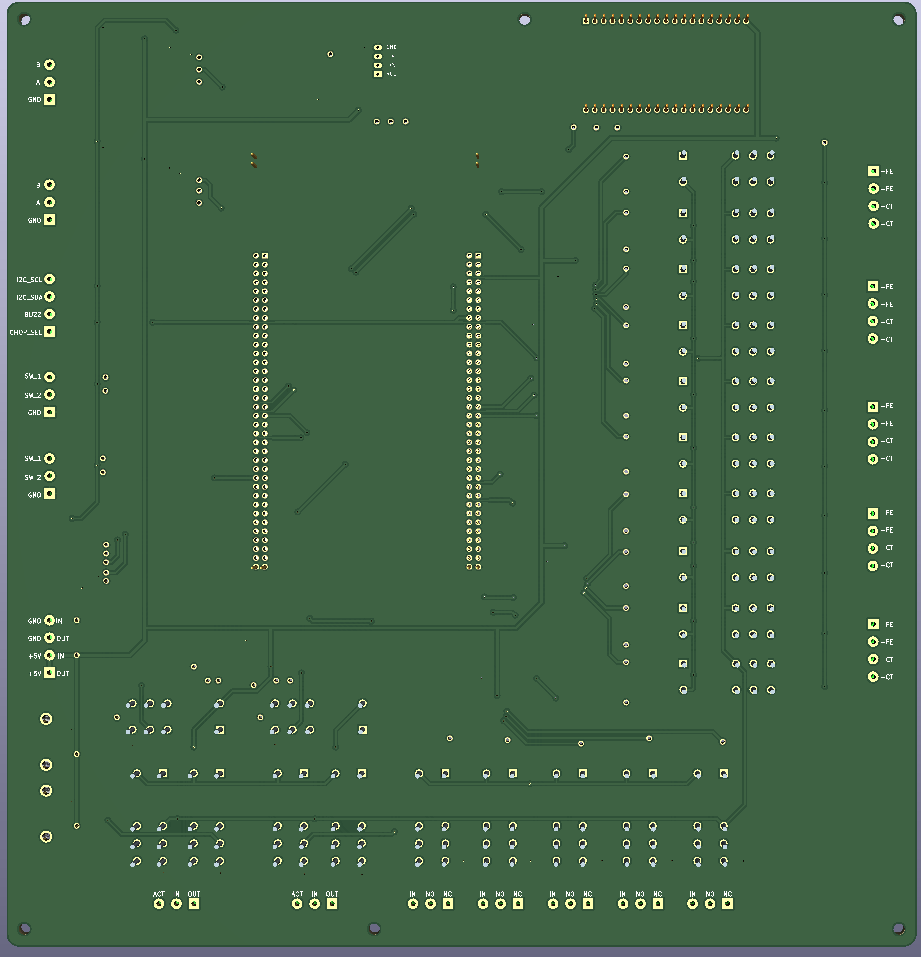
hardware/salt/temp_files/8.png
