martinanus/salt/hardware/salt_ihm/temp_files/Screenshot from 2024-06-09 23-31-38.png

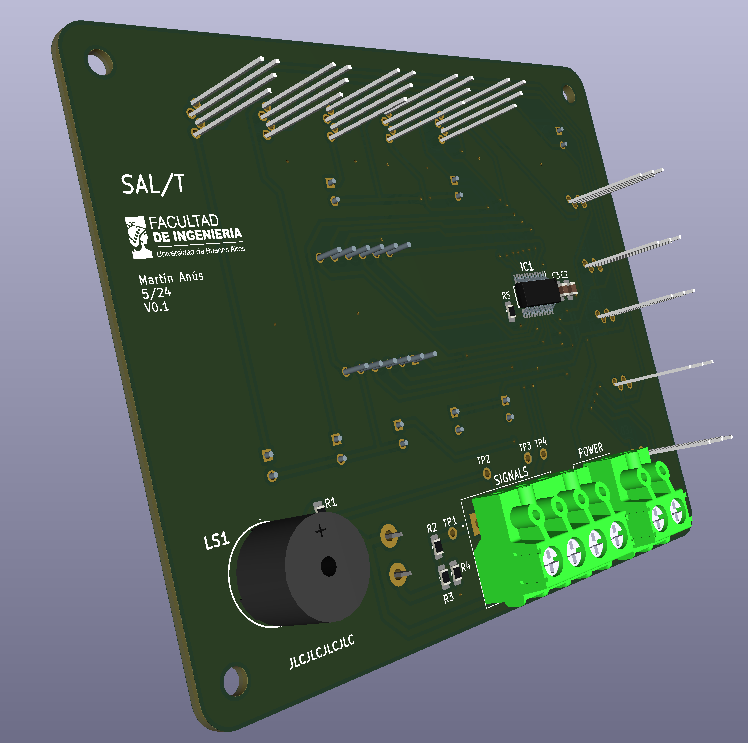
hardware/salt_ihm/temp_files/Screenshot from 2024-06-09 23-31-38.png
