martinanus/salt/hardware/salt_ihm/temp_files/Screenshot from 2024-06-09 23-32-39.png

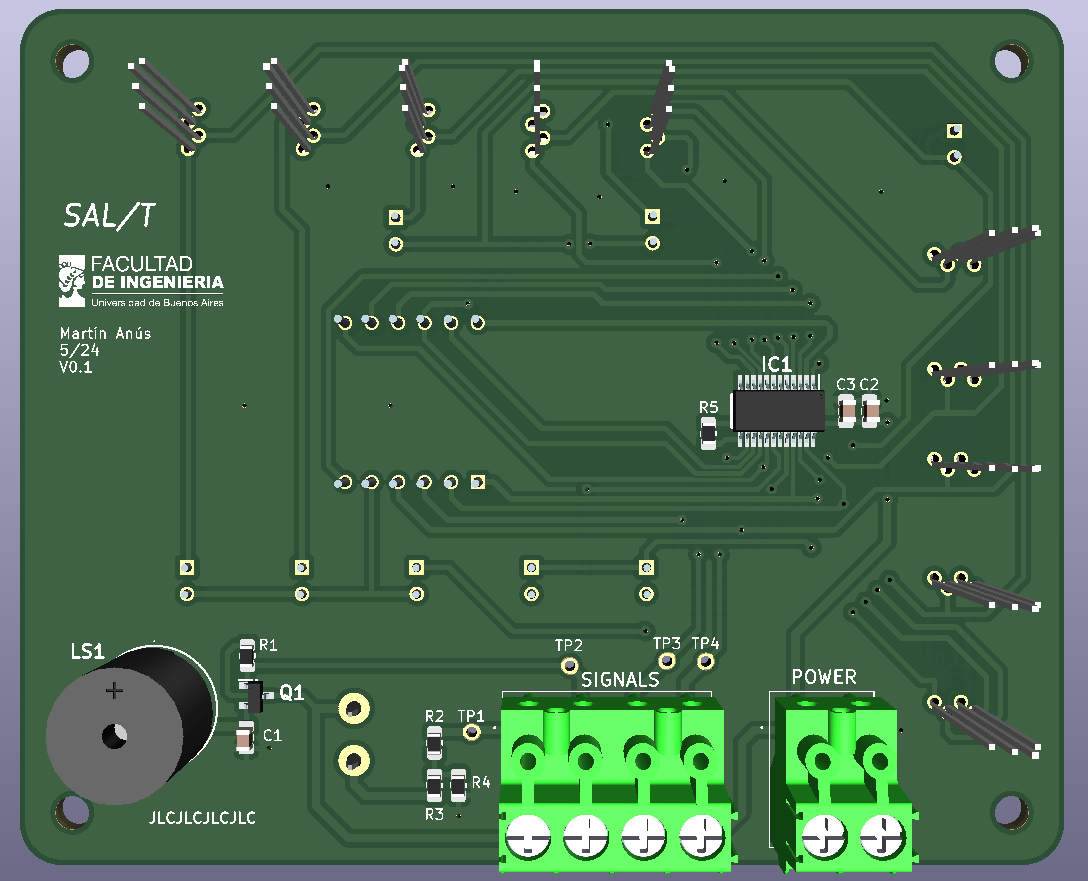
hardware/salt_ihm/temp_files/Screenshot from 2024-06-09 23-32-39.png
