martinanus/salt/hardware/salt/Models/WP7113LZGCK/WP7113GC.stp

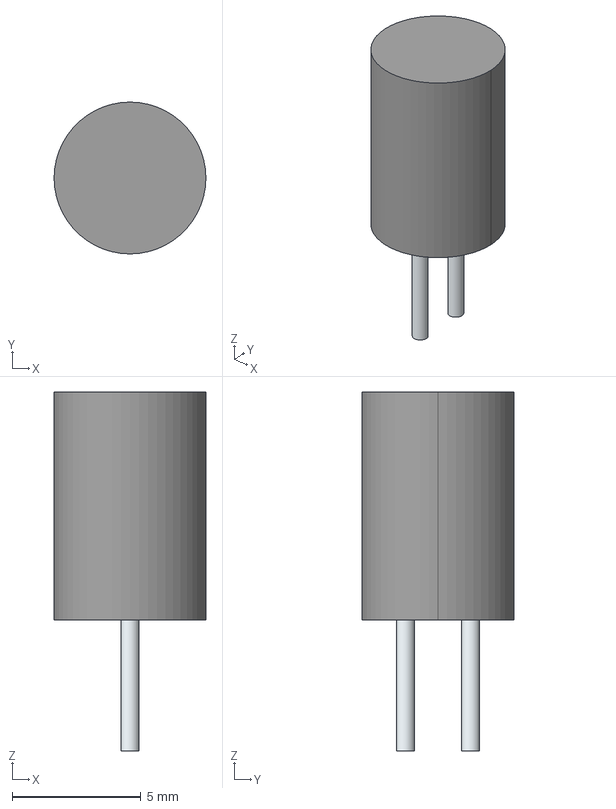
[picture p78: CAD file, 2024-11-01]
hardware/salt/Models/WP7113LZGCK/WP7113GC.stp
5.90 x 5.90 x 13.9 mm
Leads x 2
