martinanus/salt/hardware/salt/Models/GY-GPS6MV2/GY-NEO6MV2.step

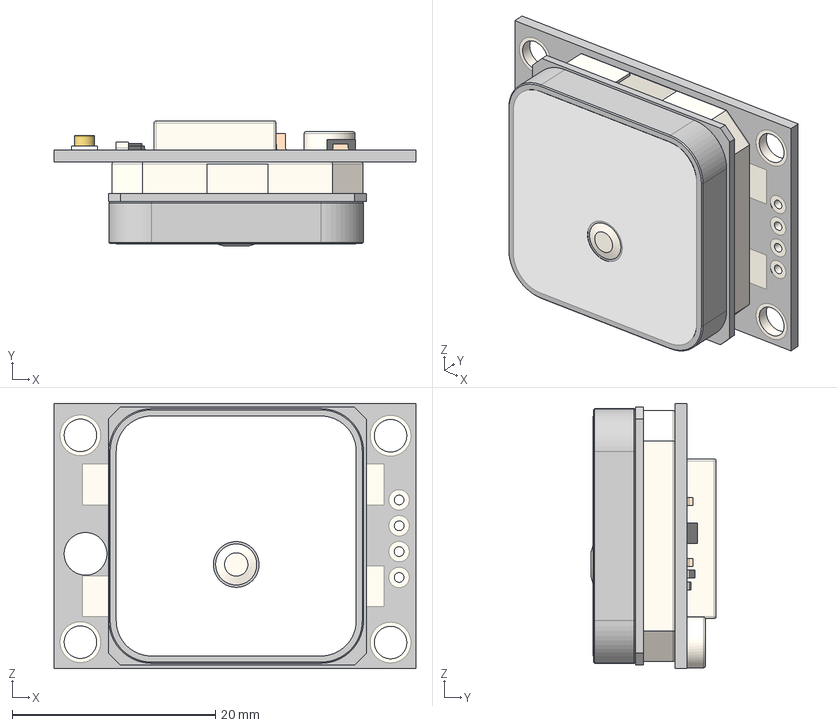
[picture p79: CAD file, 2024-11-01]
hardware/salt/Models/GY-GPS6MV2/GY-NEO6MV2.step
35.6 x 12.3 x 26.1 mm
GPS_ublox_board
GPS_board
GPS_ant
GPS_back
