martinanus/salt/documentacion/Informe de tesis/src/img/gabinete_fabricado.jpeg

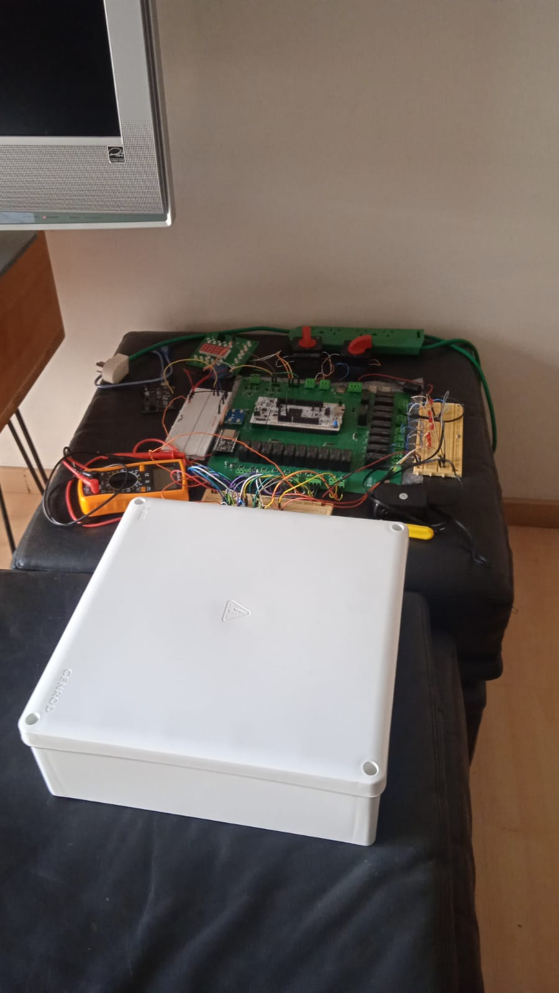
documentacion/Informe de tesis/src/img/gabinete_fabricado.jpeg
