martinanus/salt/documentacion/Informe de tesis/src/4 - Ensayos y resultados/4.0 - intro.tex

En este capítulo se presenta el banco de pruebas utilizado para realizar los ensayos del sistema y los resultados obtenidos de las pruebas  tanto a nivel hardware y firmware por separado como de manera integral, permitiendo validar todas las funcionalidades del sistema.
