martinanus/salt/hardware/salt_ihm/salt_ihm_pdfs/Esquematico/salt_ihm-Esquematico.pdf

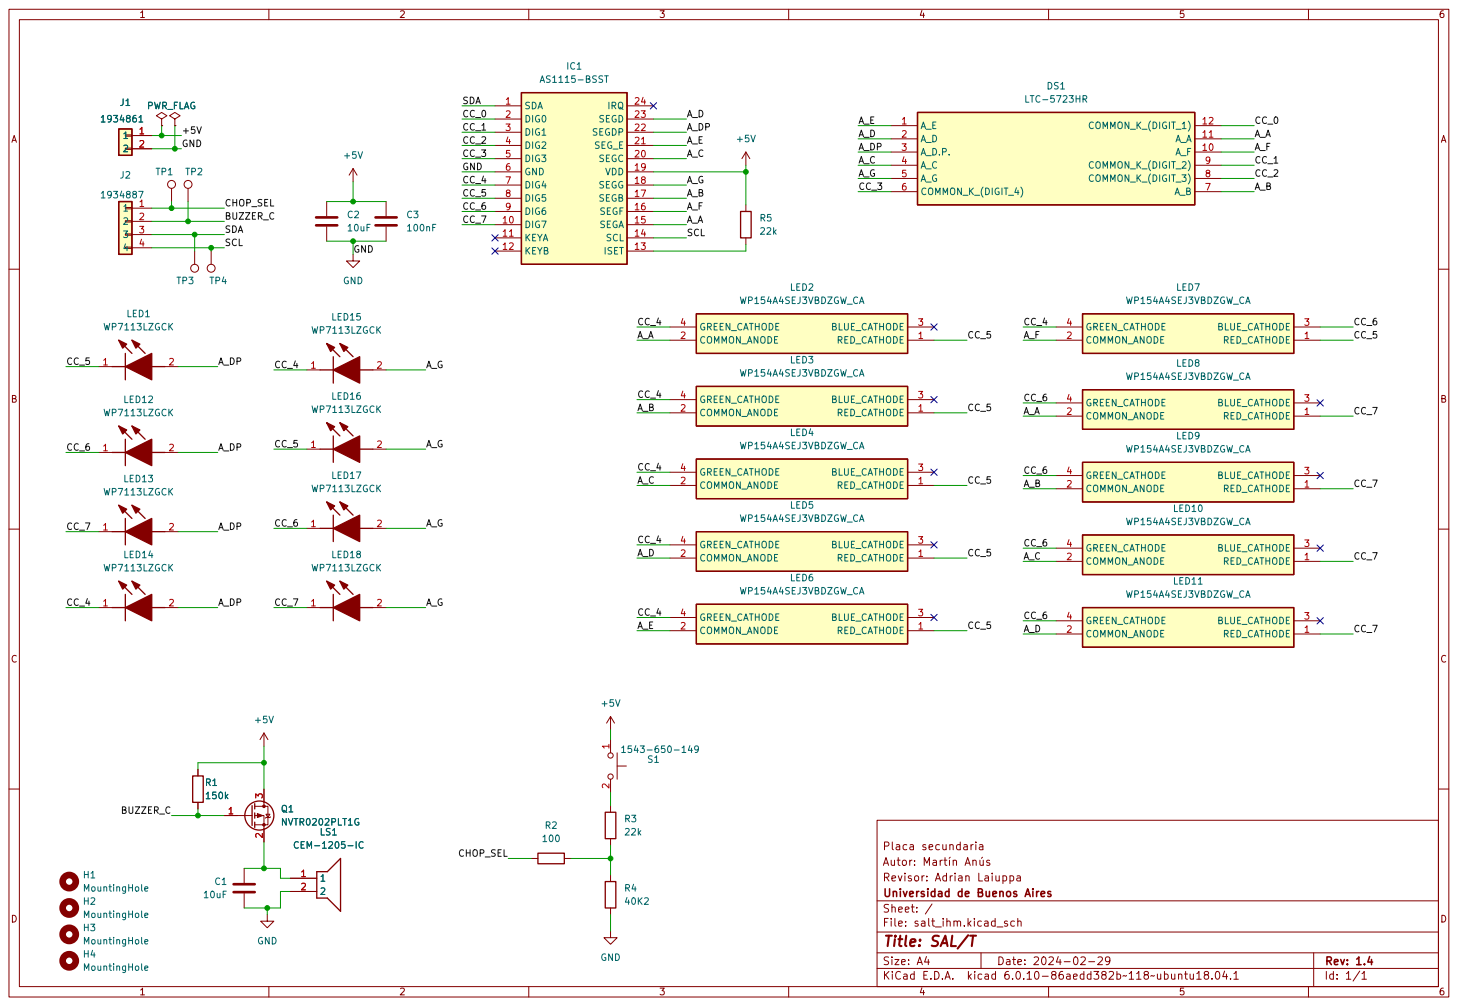
[picture p94: page 1]

File: salt_ihm.kicad_sch Sheet: / Universidad de Buenos Aires Revisor: Adrian Laiuppa
