martinanus/salt/hardware/salt/salt_pdfs/PCB/Layers/salt-B_Cu.pdf

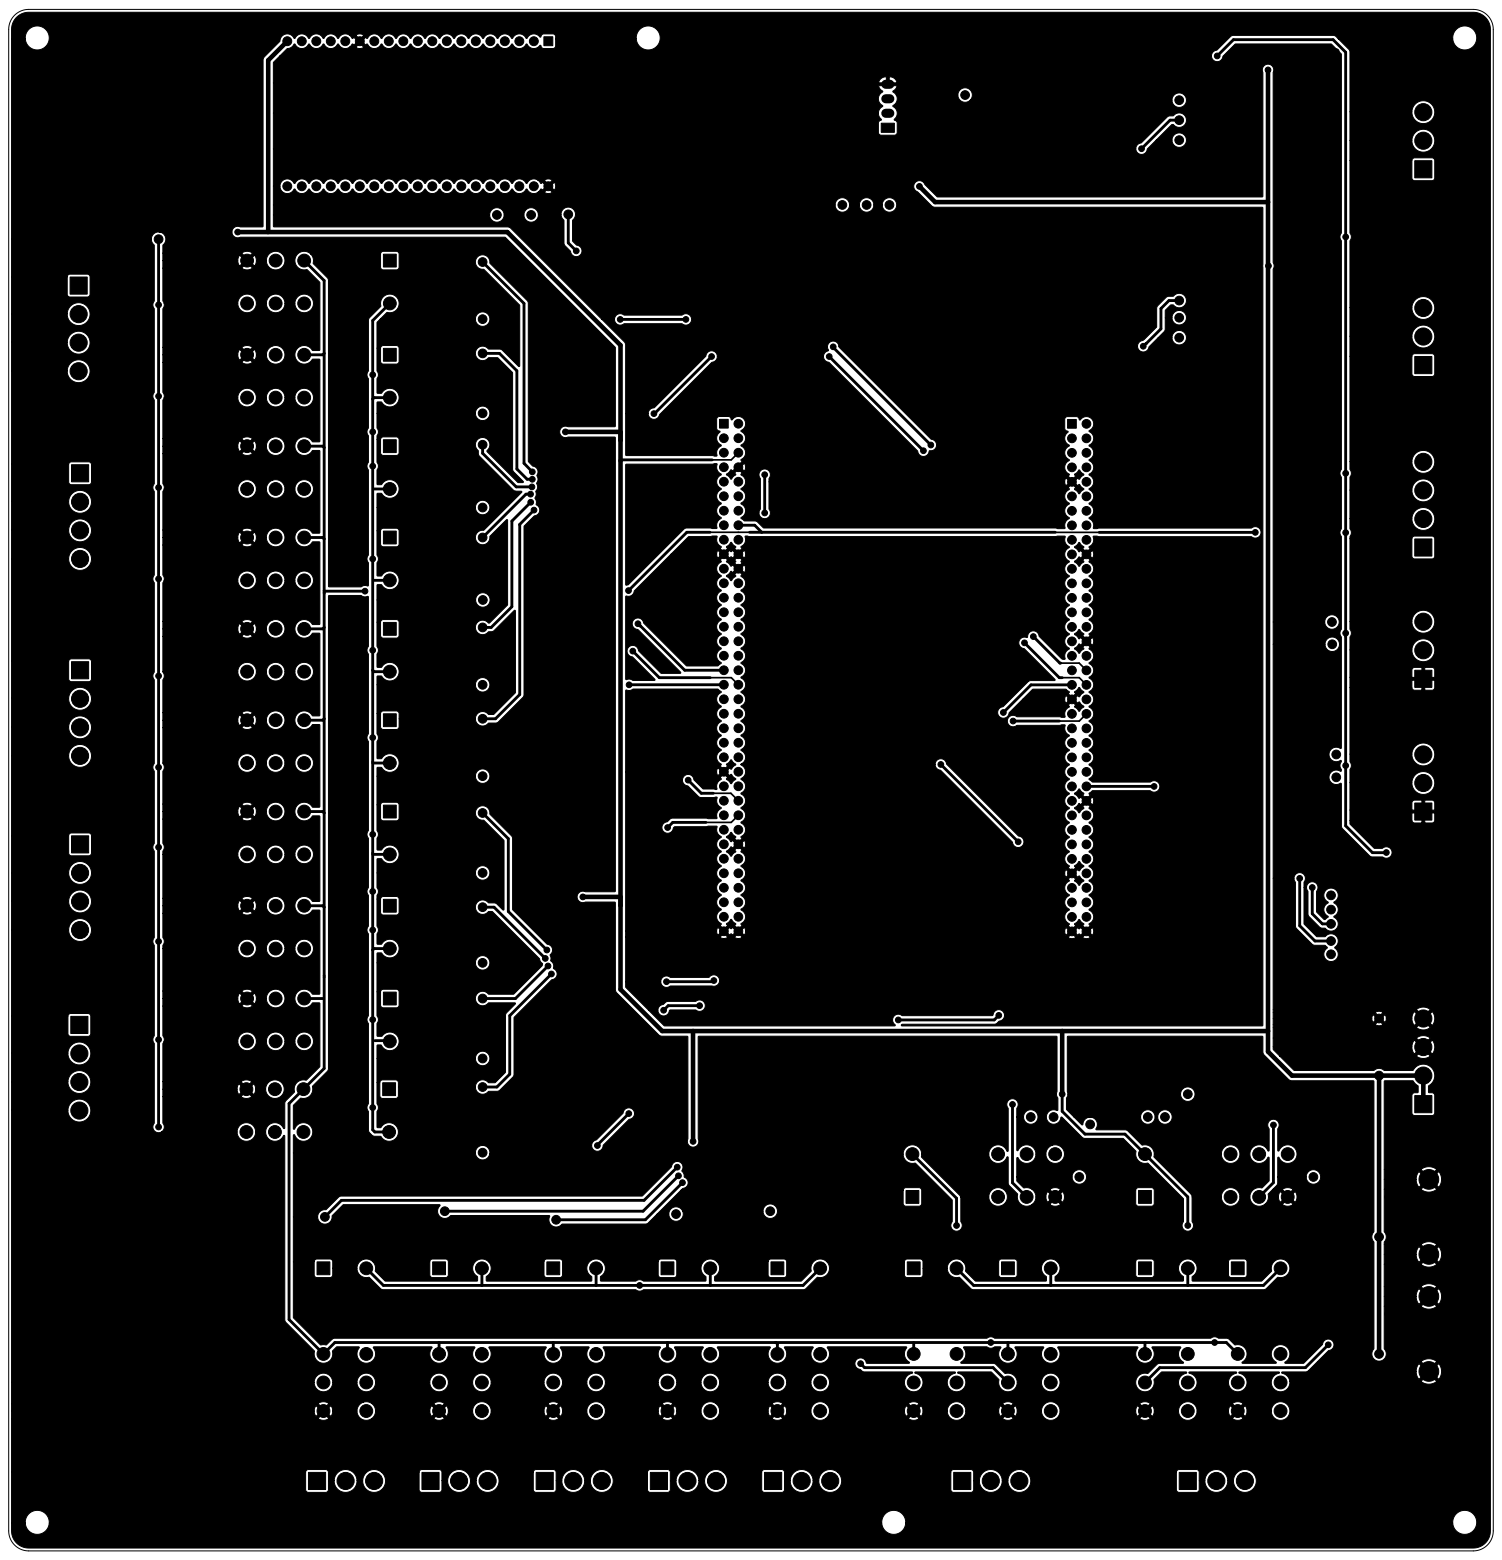
[picture p103: page 1]
