martinanus/salt/hardware/salt/salt_pdfs/PCB/Layers/salt-B_Mask.pdf

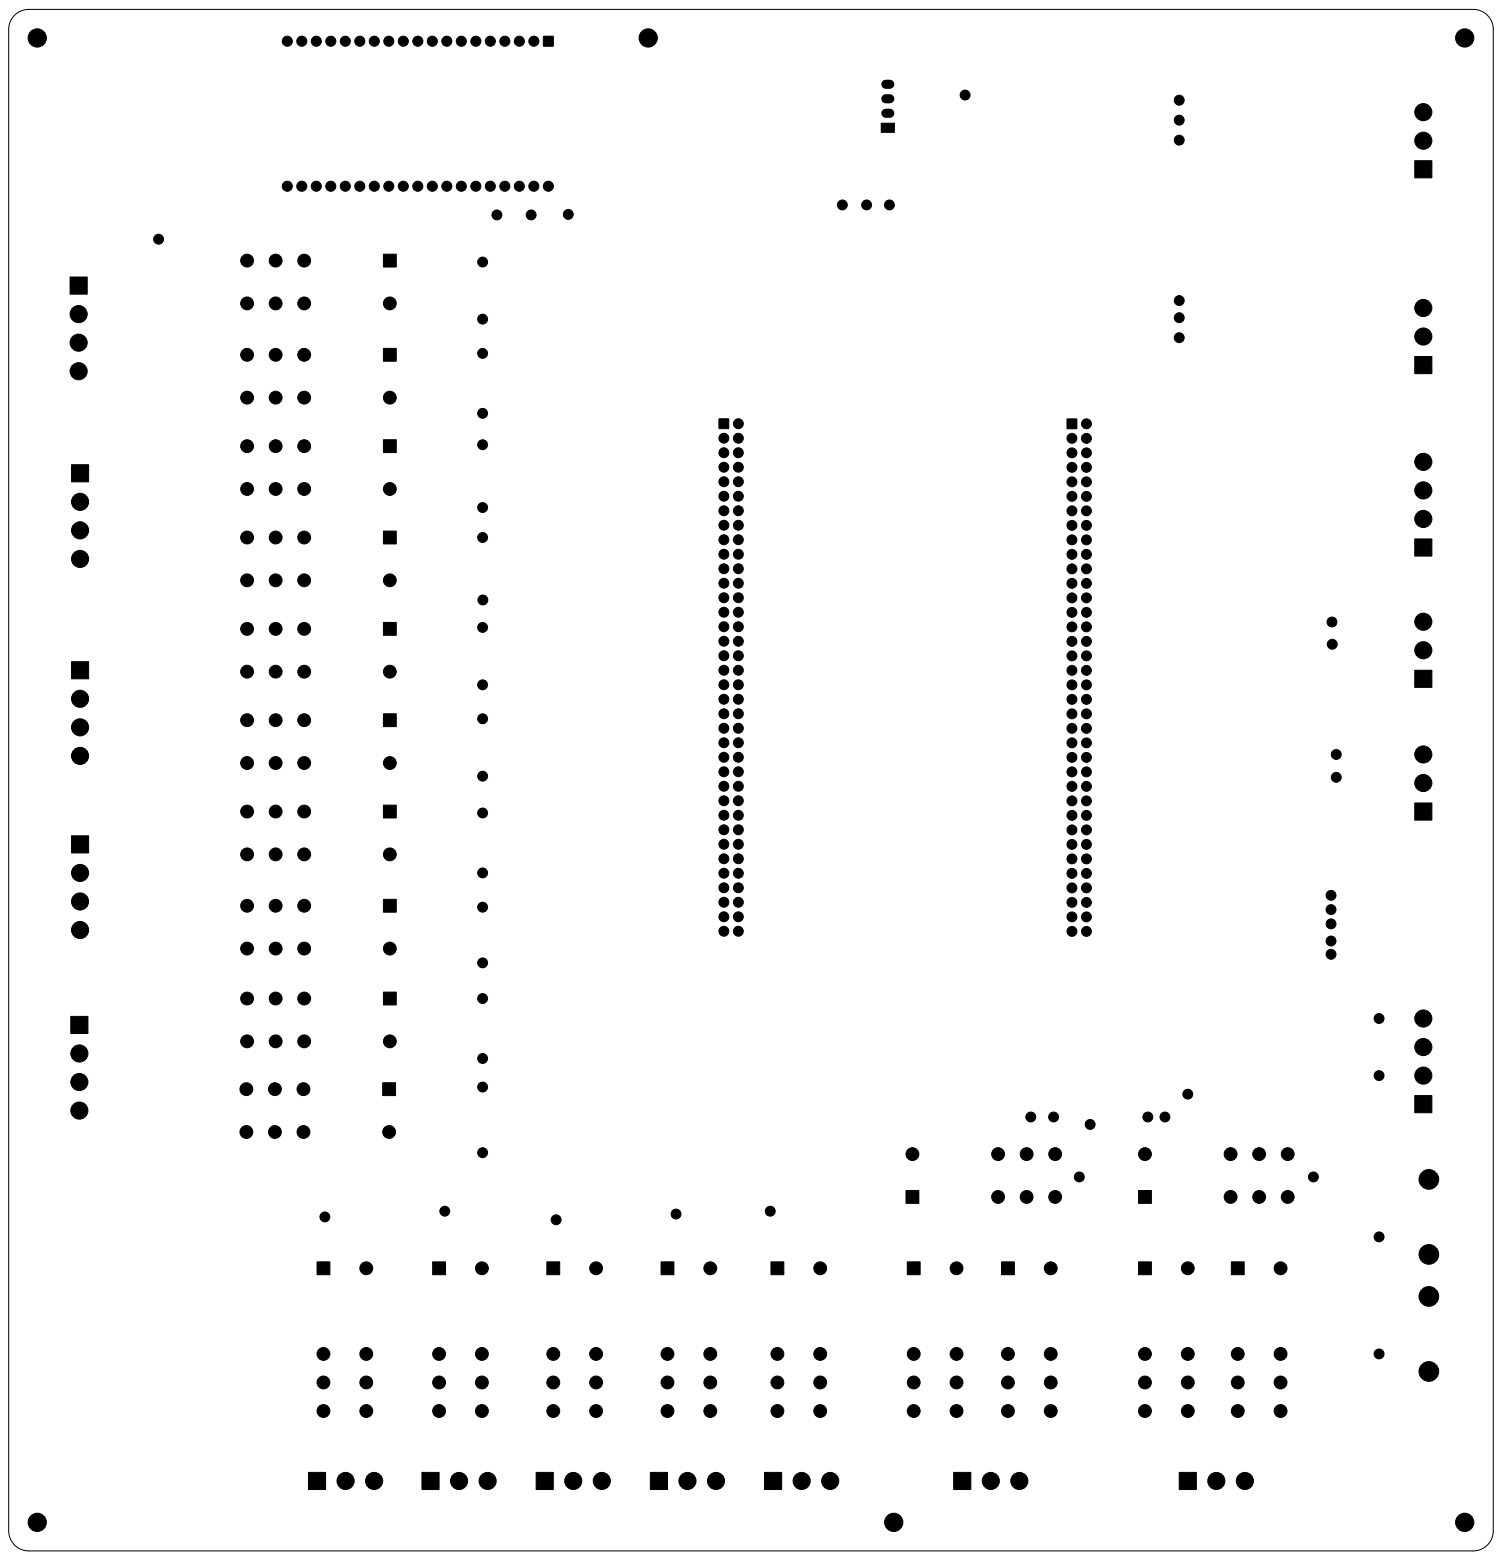
[picture p104: page 1]
