martinanus/salt/hardware/salt/salt_pdfs/PCB/Layers/salt-B_Paste.pdf

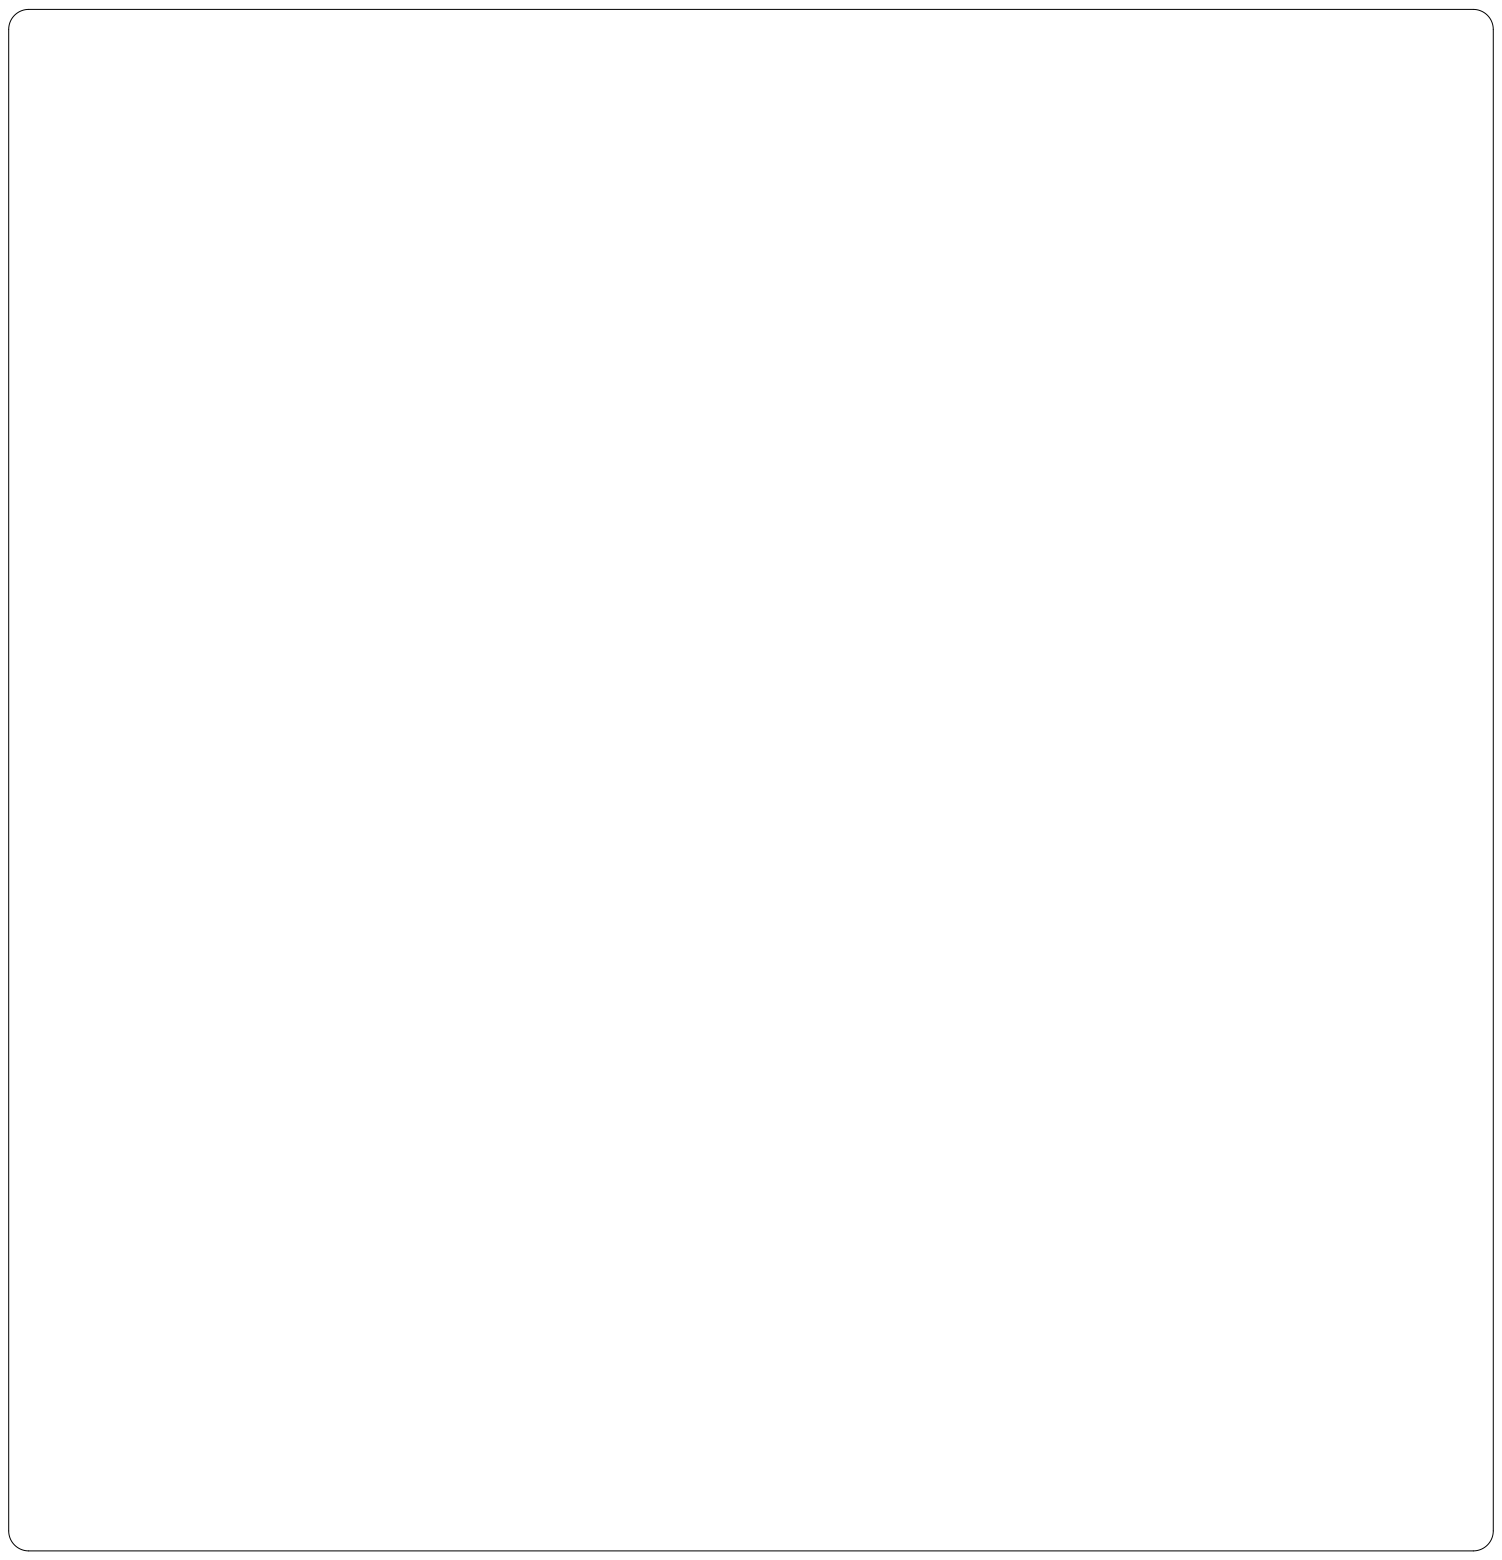
[picture p105: page 1]
