martinanus/salt/hardware/salt/salt_pdfs/PCB/Layers/salt-B_Silkscreen.pdf

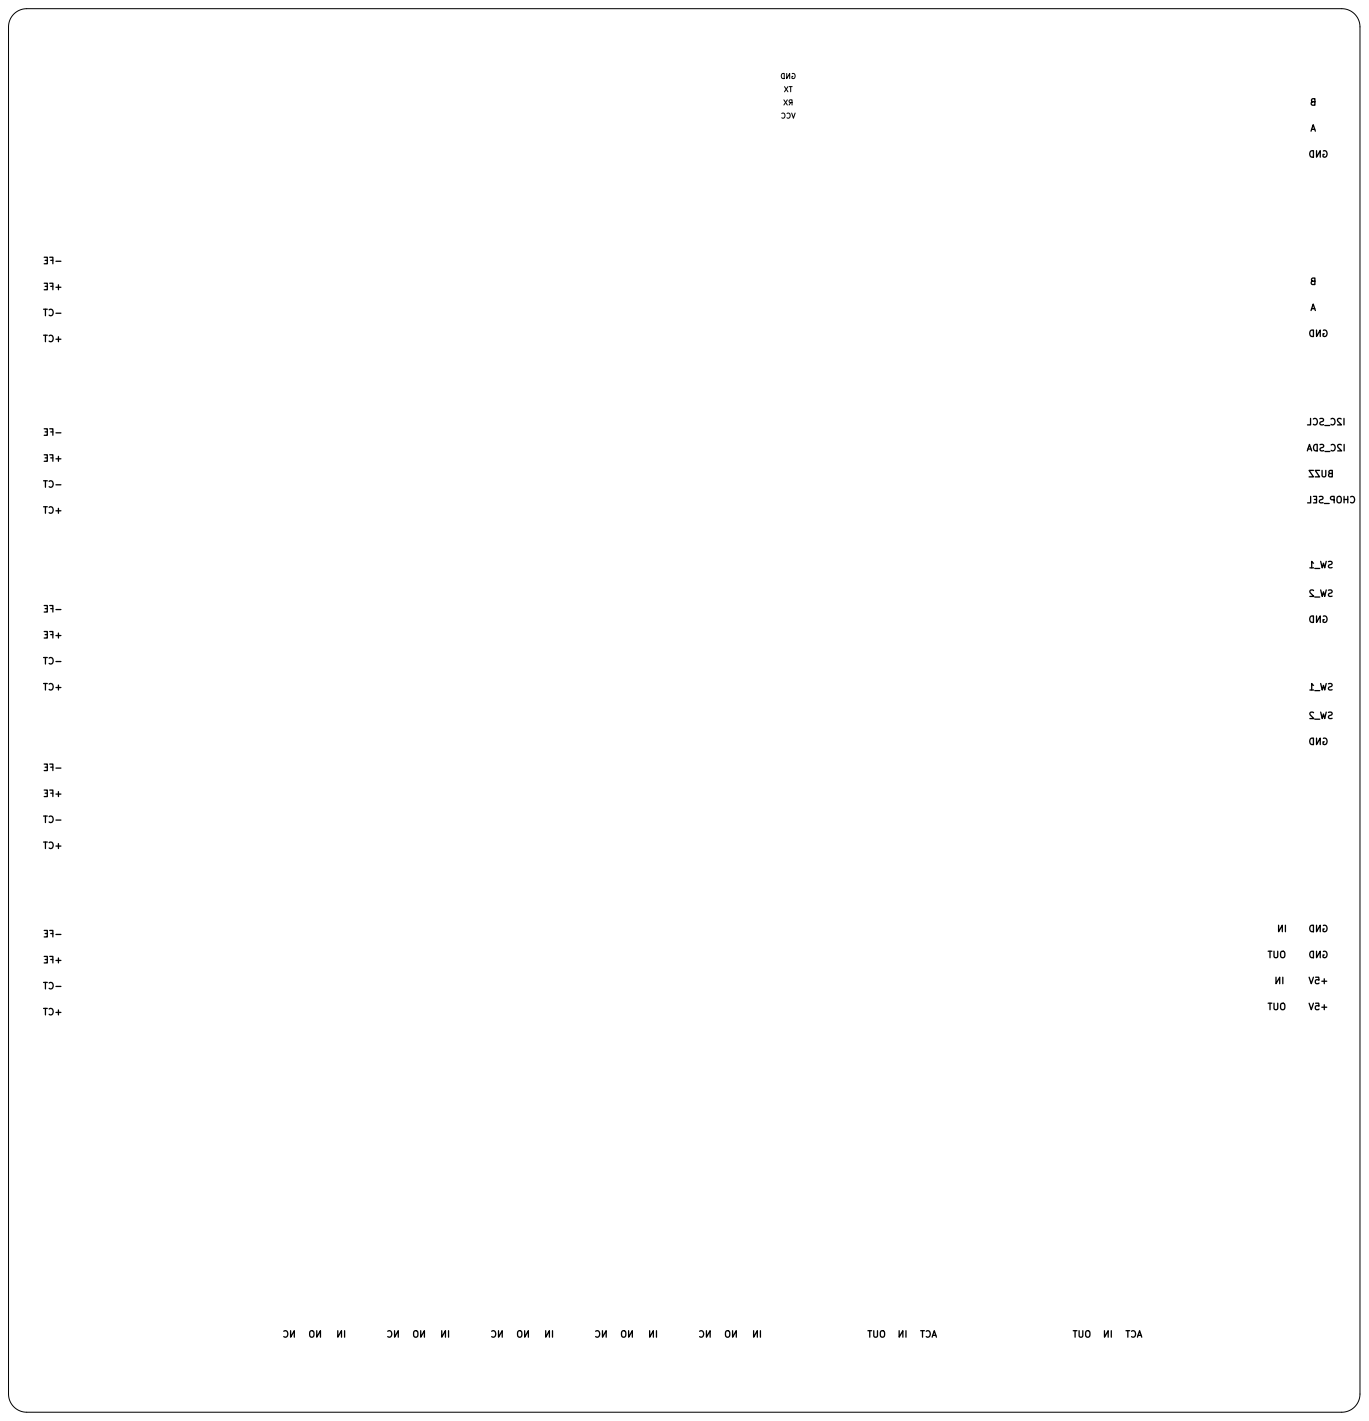
[picture p106: page 1]
