martinanus/salt/hardware/salt/salt_pdfs/PCB/Layers/salt-F_Cu.pdf

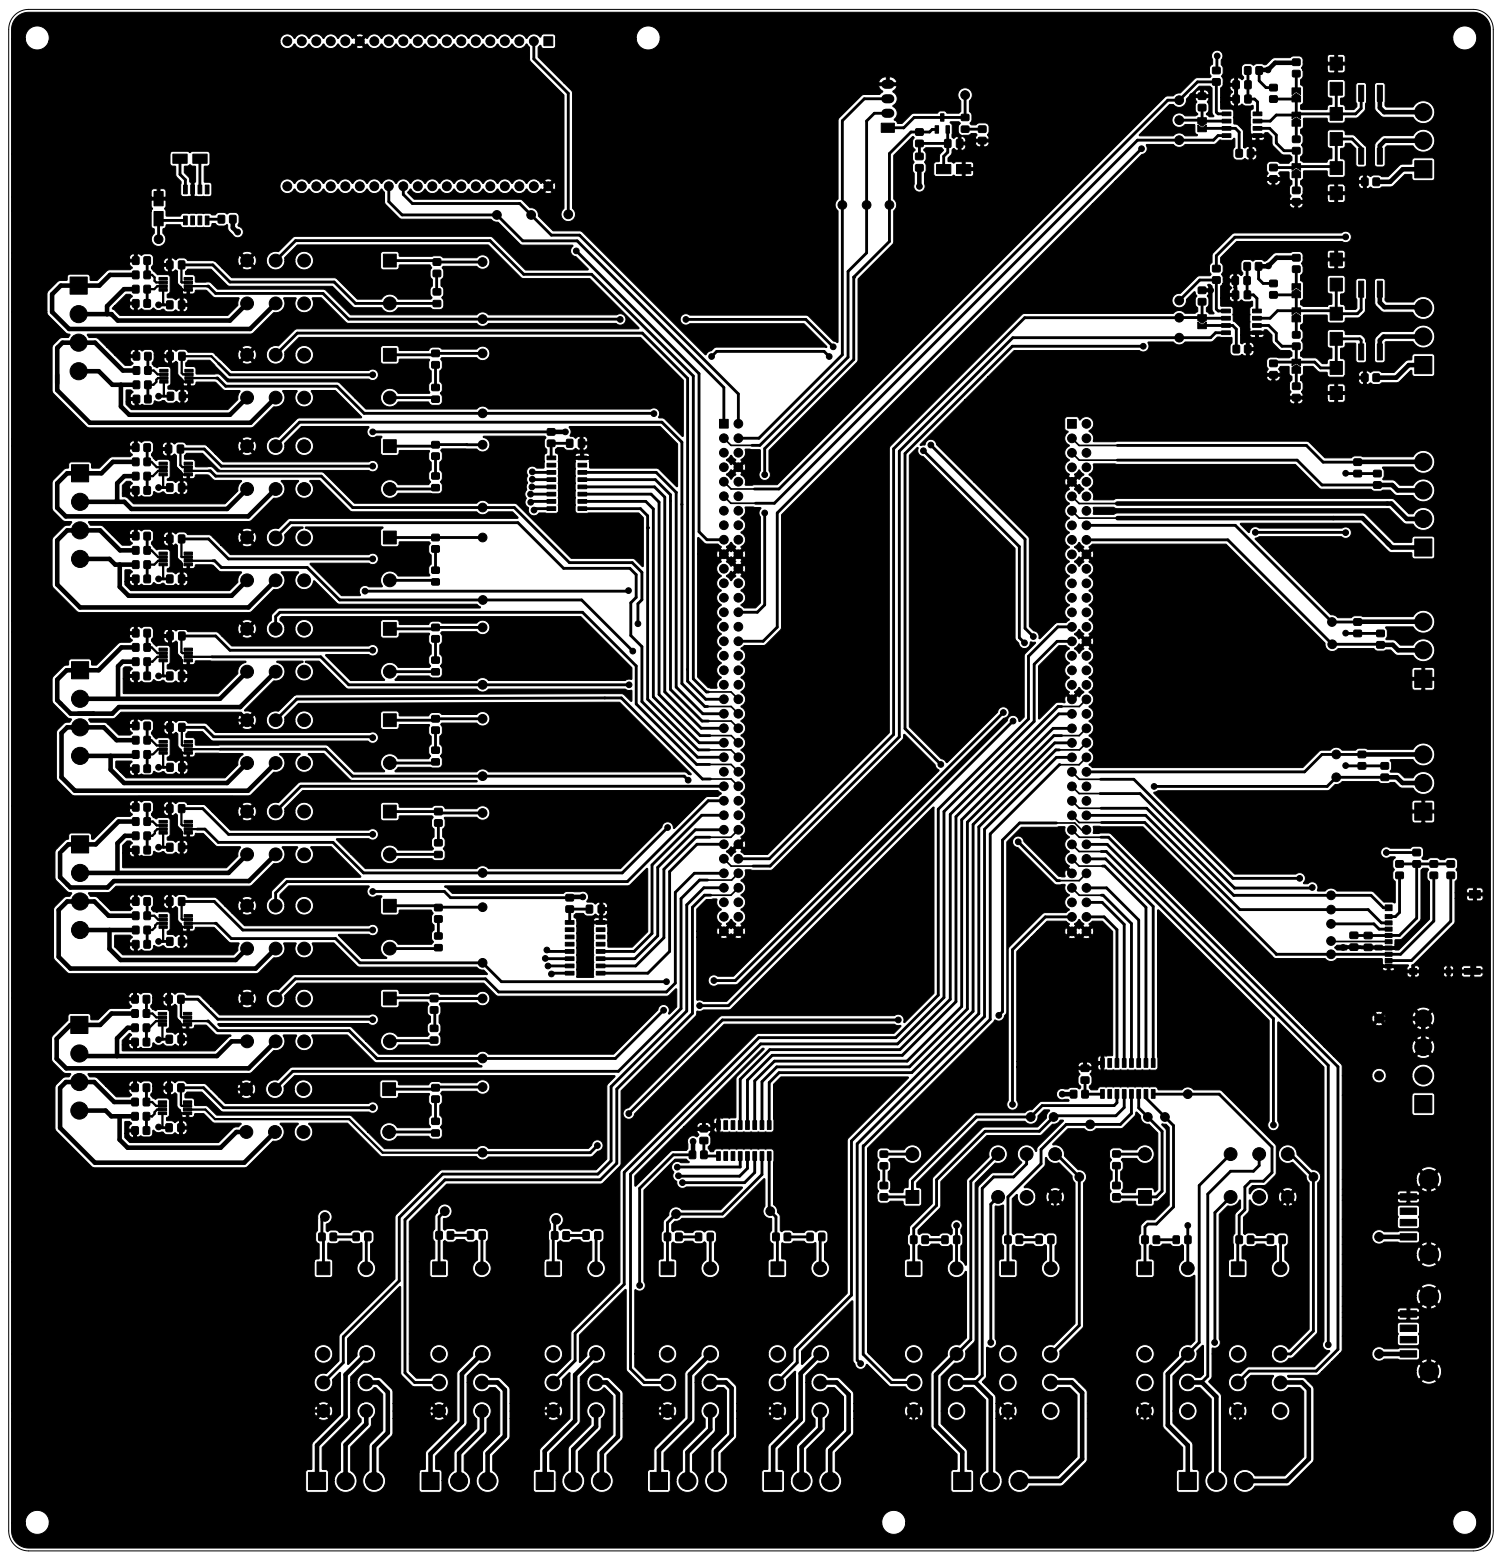
[picture p107: page 1]
