martinanus/salt/hardware/salt/salt_pdfs/PCB/Layers/salt-F_Mask.pdf

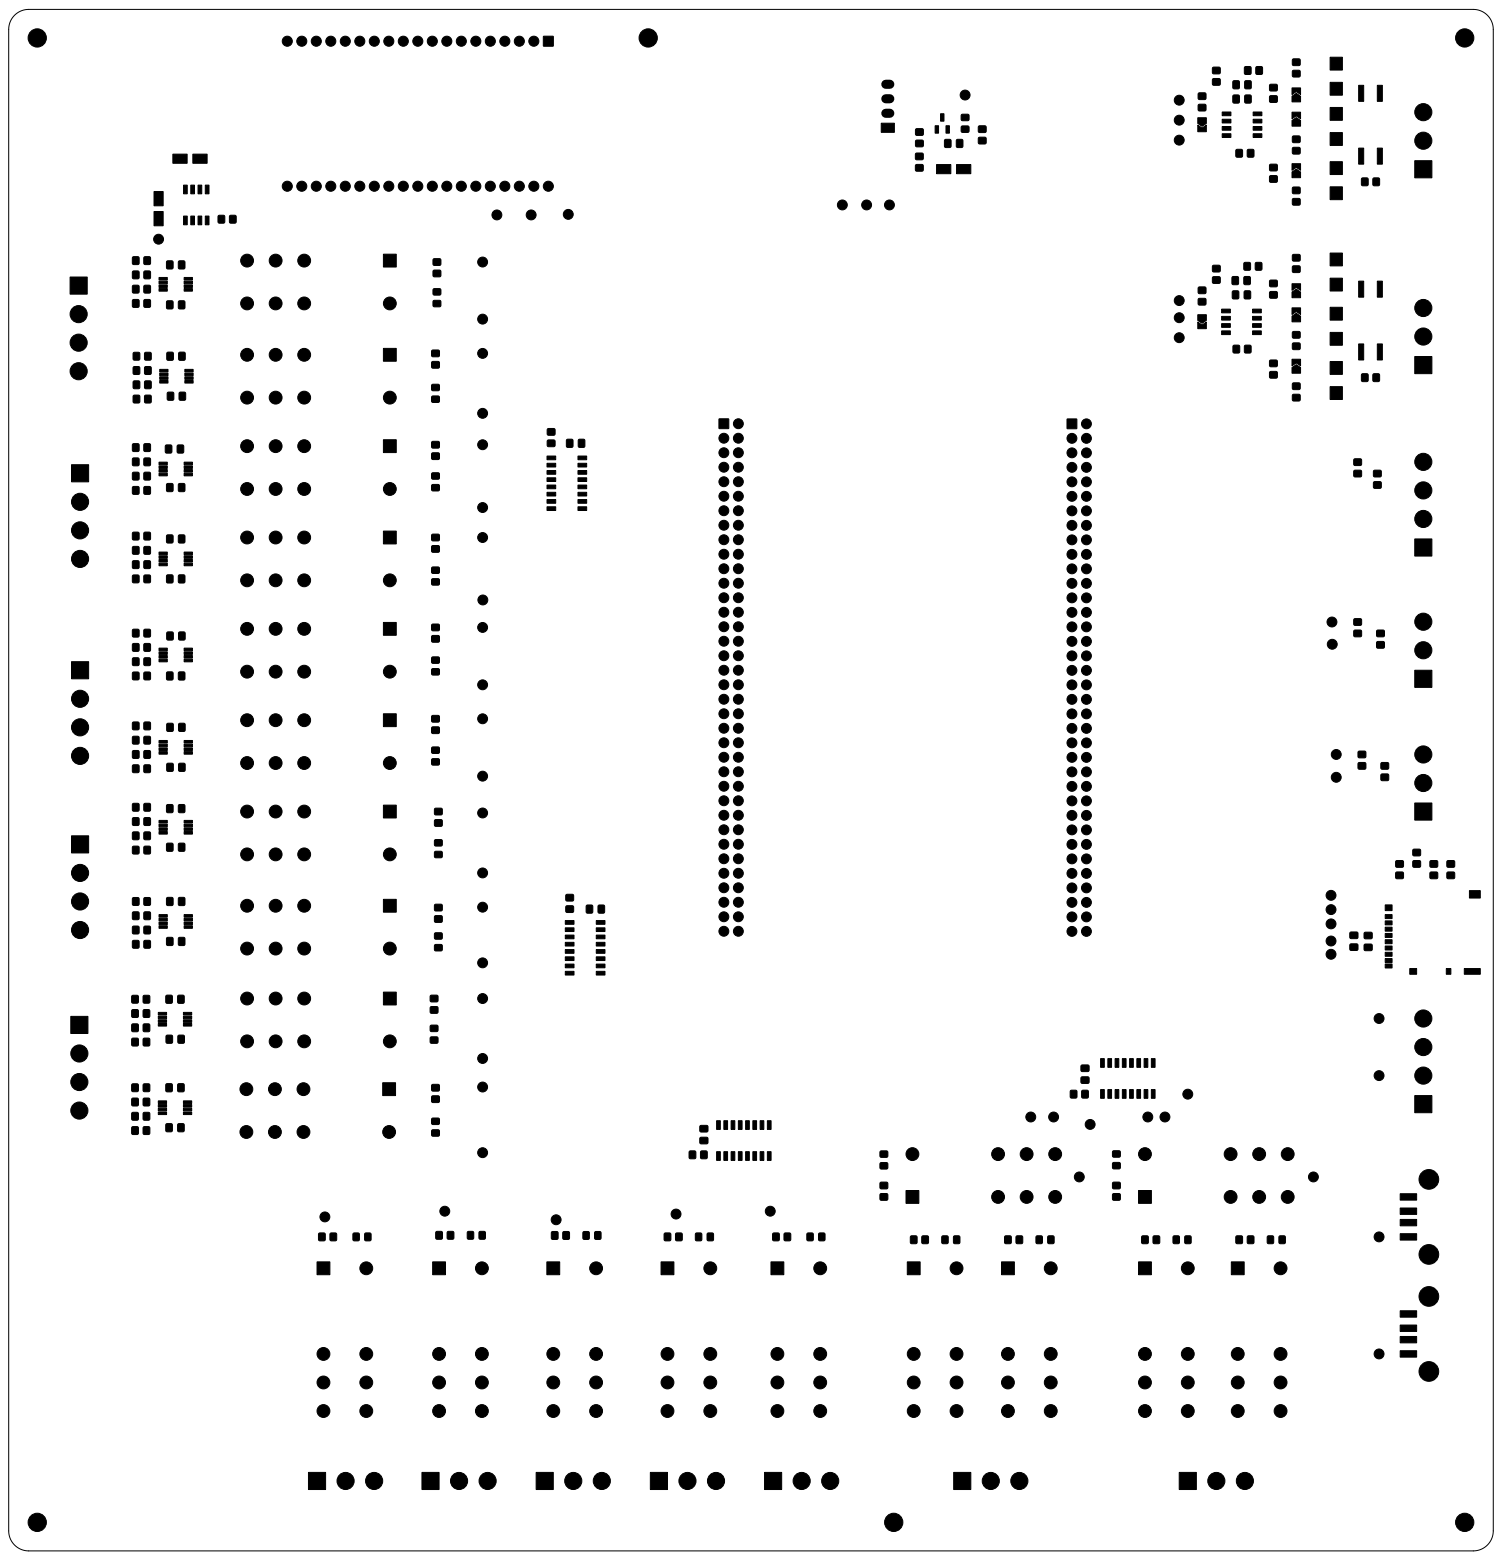
[picture p108: page 1]
