martinanus/salt/hardware/salt/salt_pdfs/PCB/Layers/salt-F_Paste.pdf

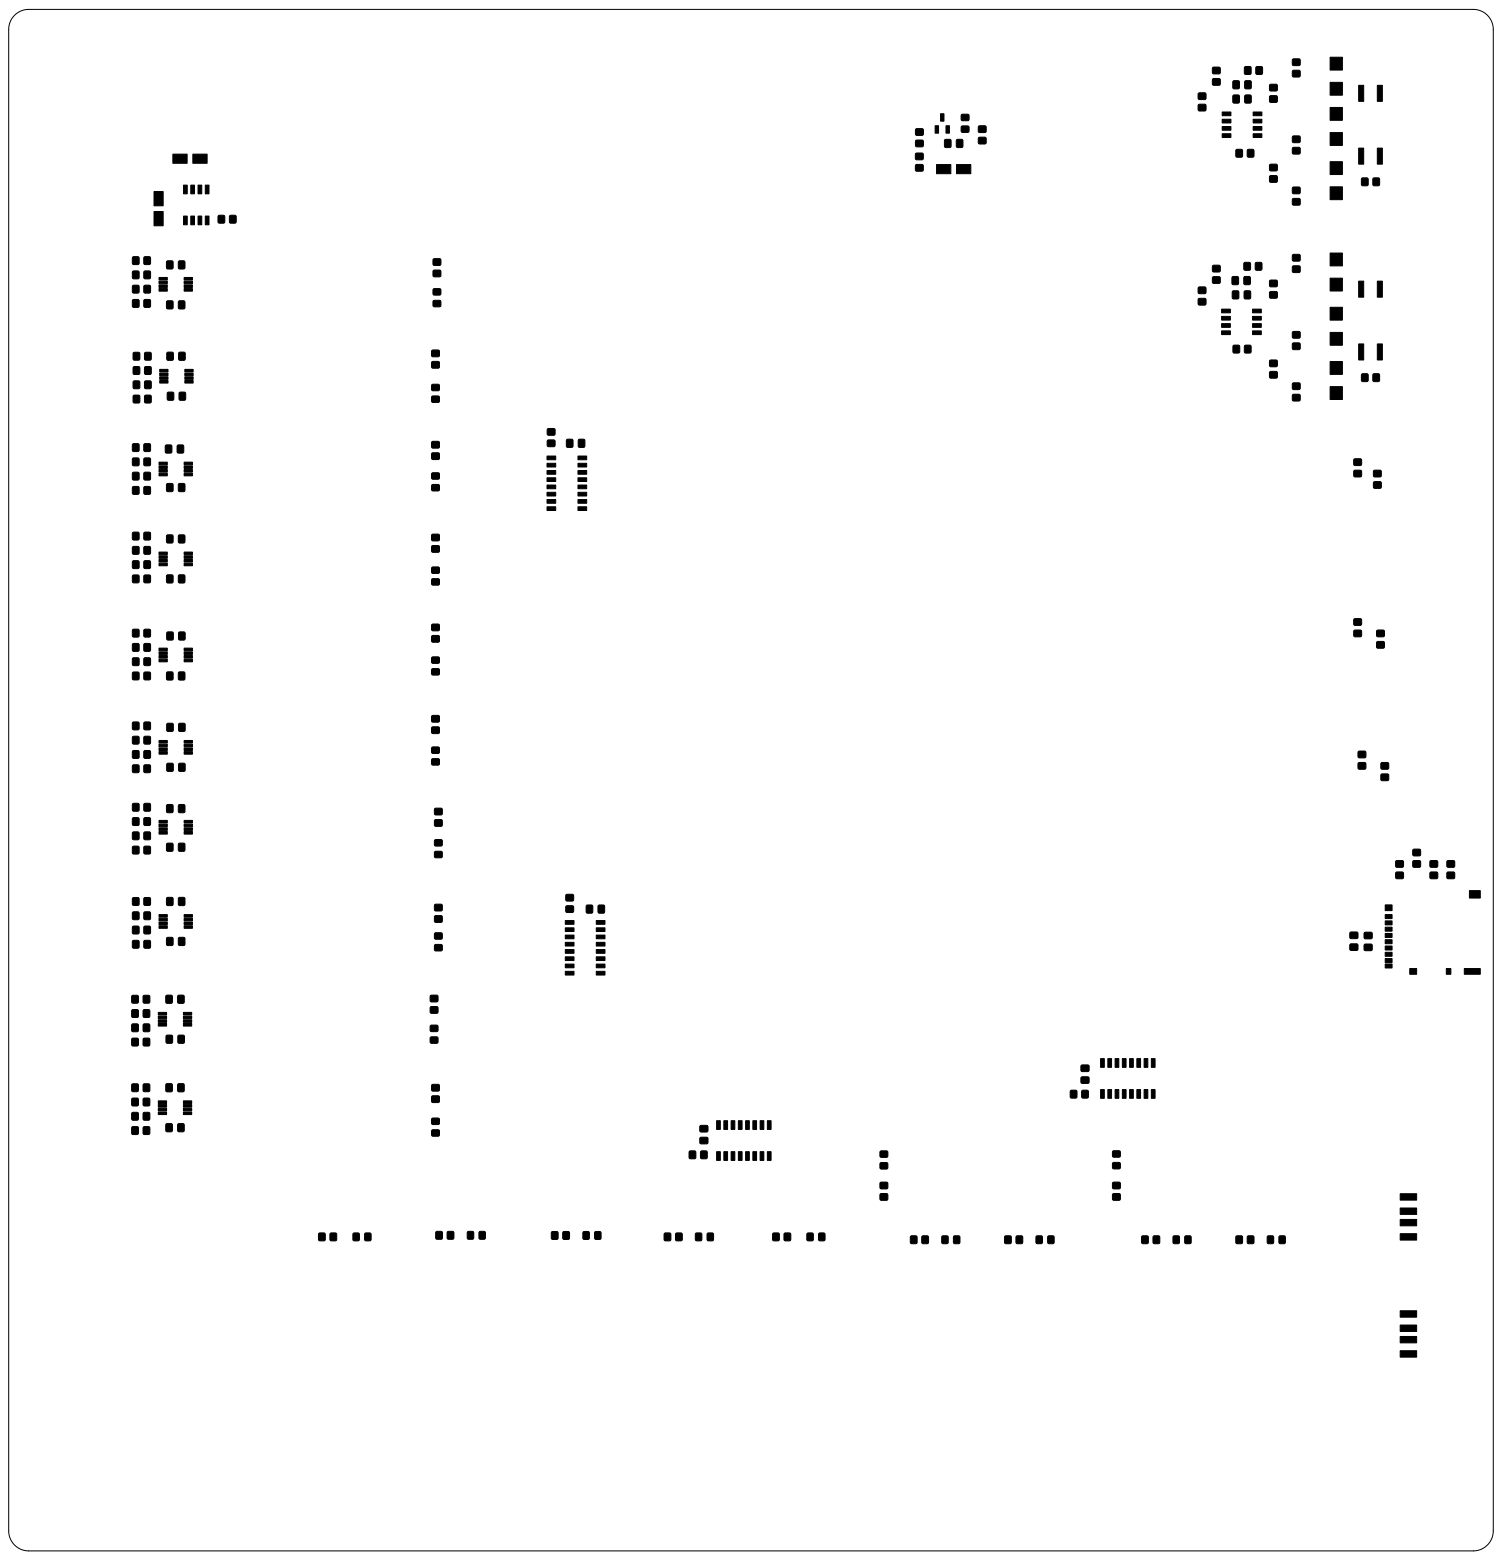
[picture p109: page 1]
