martinanus/salt/hardware/salt/salt_pdfs/PCB/Layers/salt-F_Silkscreen.pdf

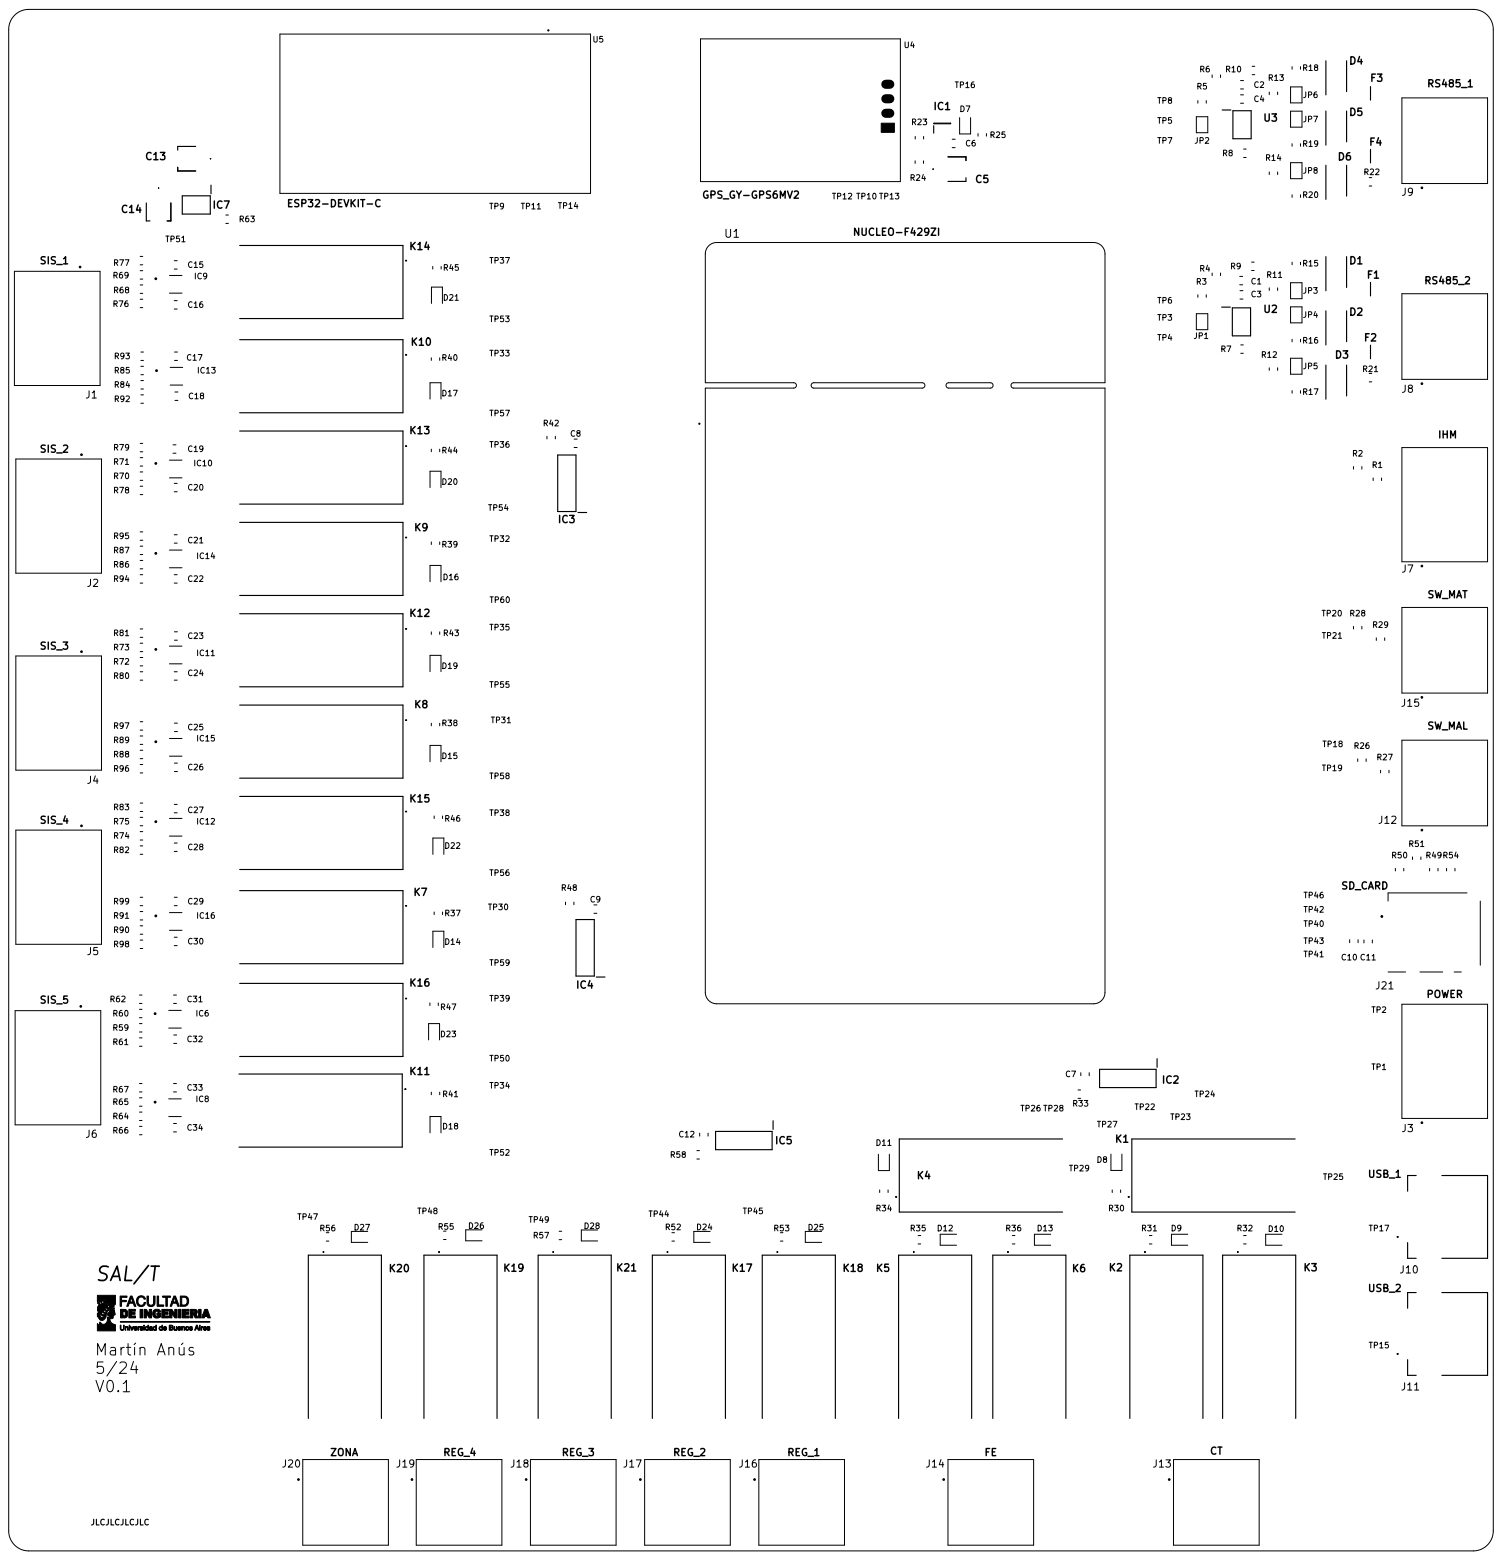
[picture p110: page 1]
