martinanus/salt/hardware/salt_ihm/salt_ihm_pdfs/PCB/Layers/salt_ihm-B_Cu.pdf

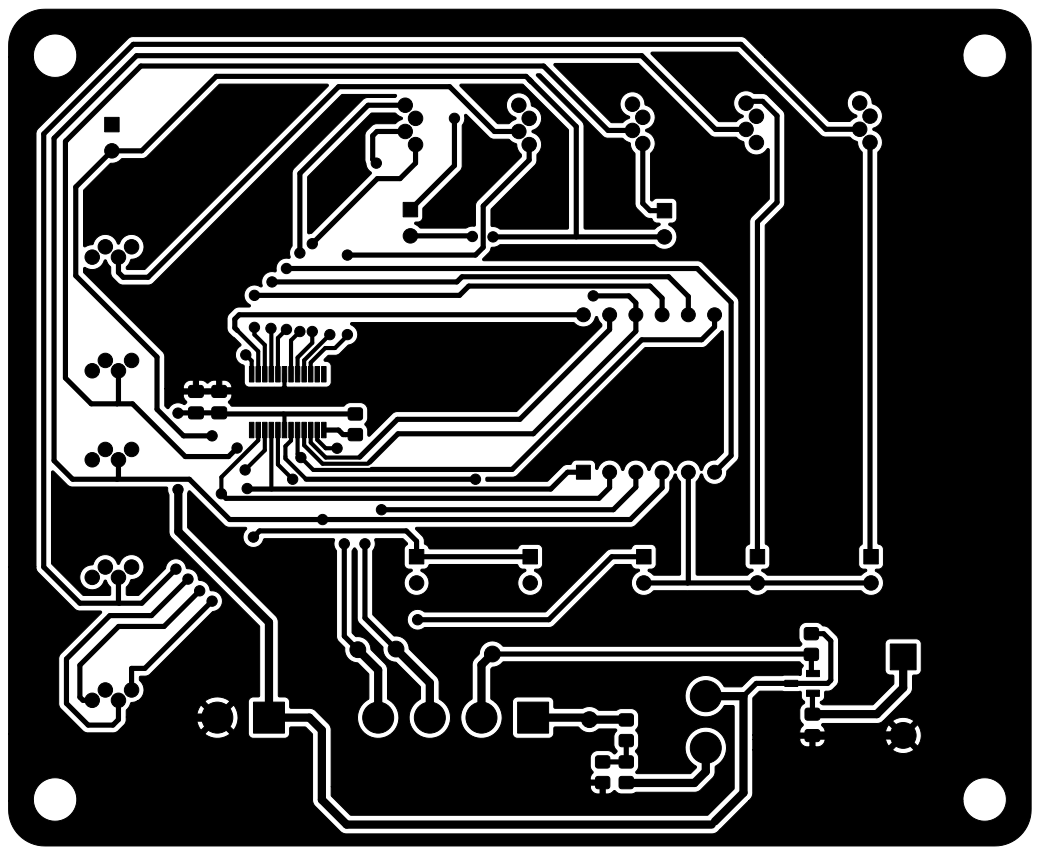
[picture p111: page 1]
