martinanus/salt/hardware/salt_ihm/salt_ihm_pdfs/PCB/Layers/salt_ihm-B_Mask.pdf

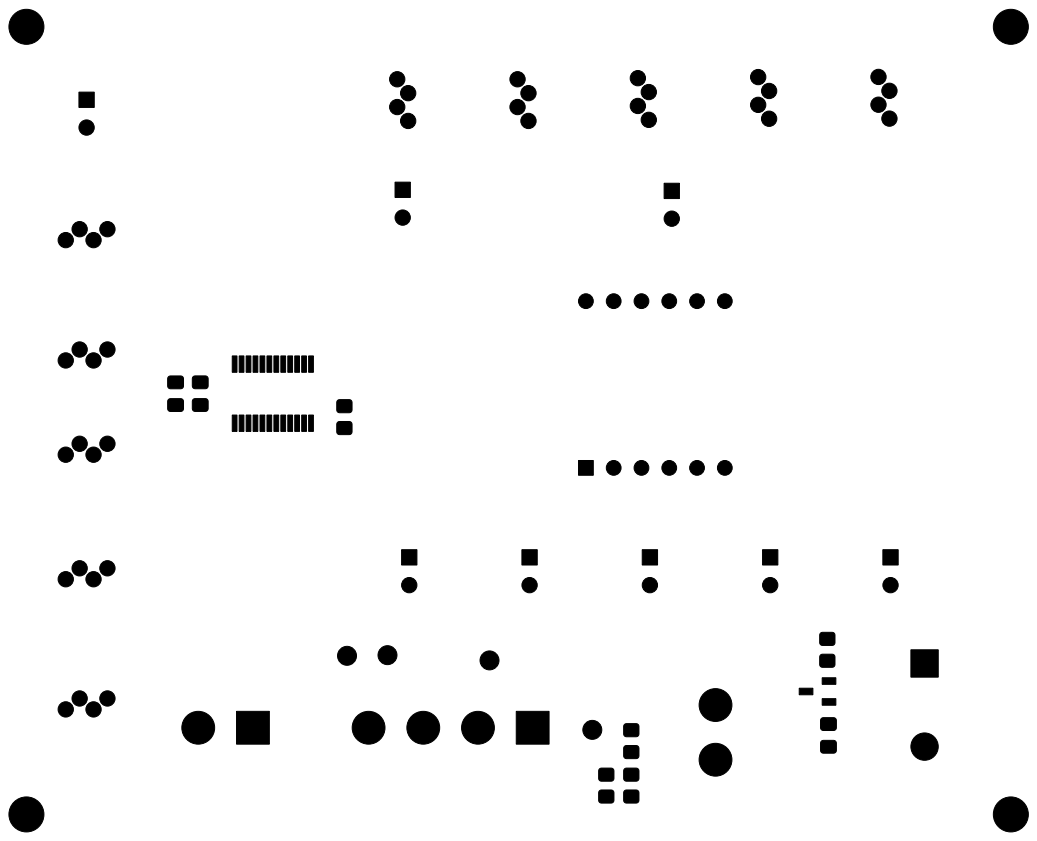
[picture p112: page 1]
