martinanus/salt/hardware/salt_ihm/salt_ihm_pdfs/PCB/Layers/salt_ihm-B_Paste.pdf

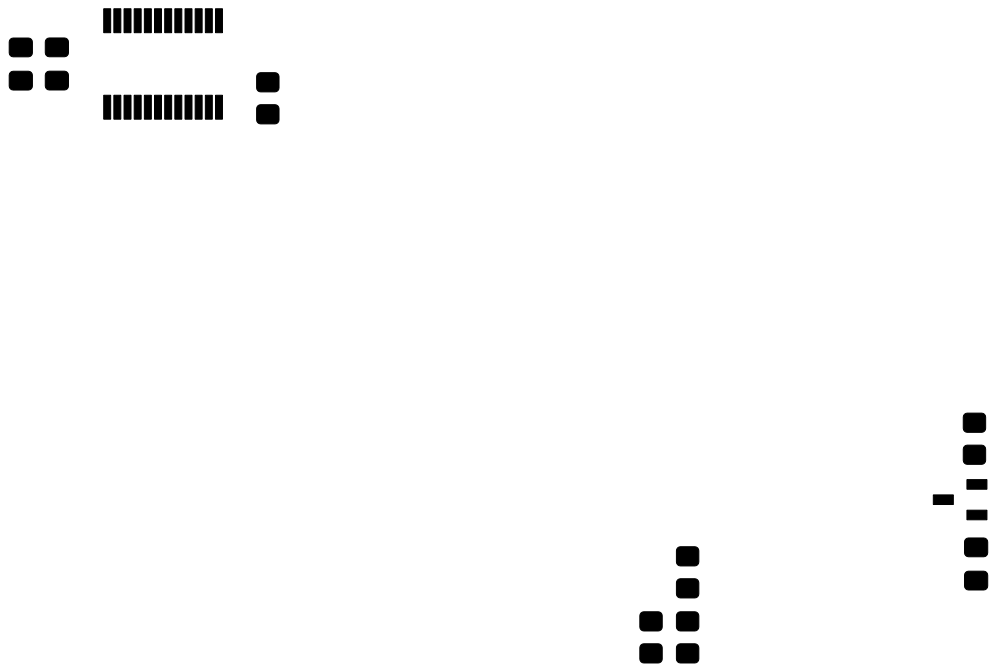
[picture p113: page 1]
