martinanus/salt/hardware/salt_ihm/salt_ihm_pdfs/PCB/Layers/salt_ihm-B_Silkscreen.pdf

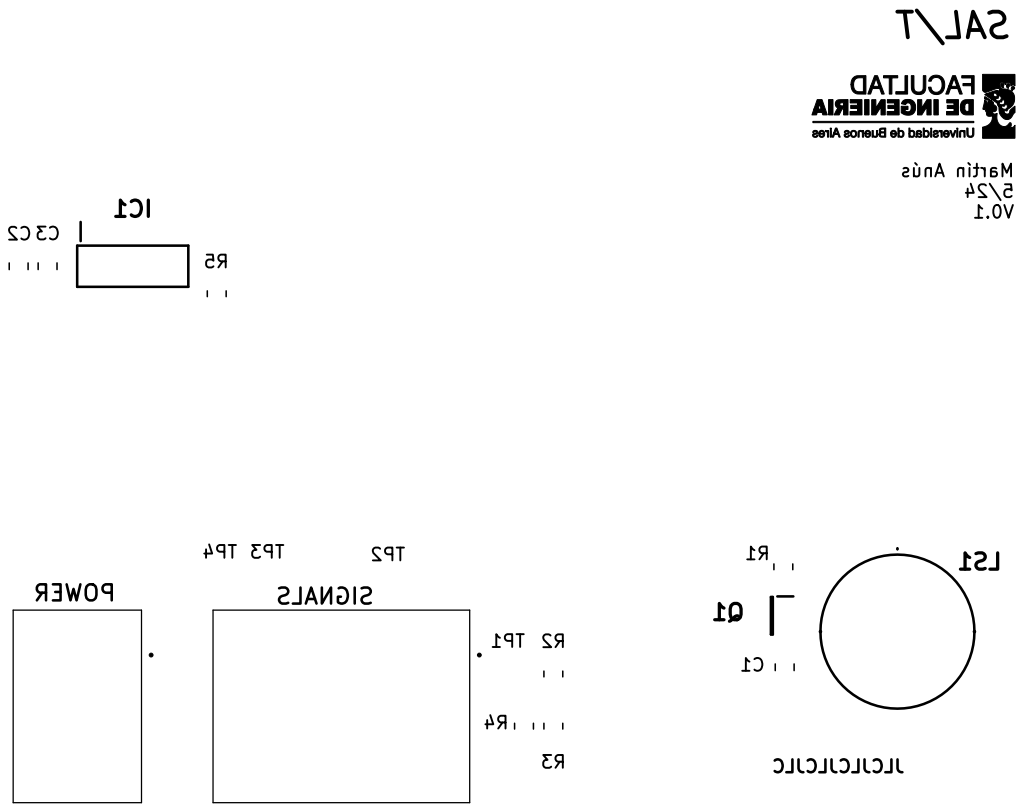
[picture p114: page 1]
