martinanus/salt/hardware/salt_ihm/salt_ihm_pdfs/PCB/Layers/salt_ihm-Edge_Cuts.pdf

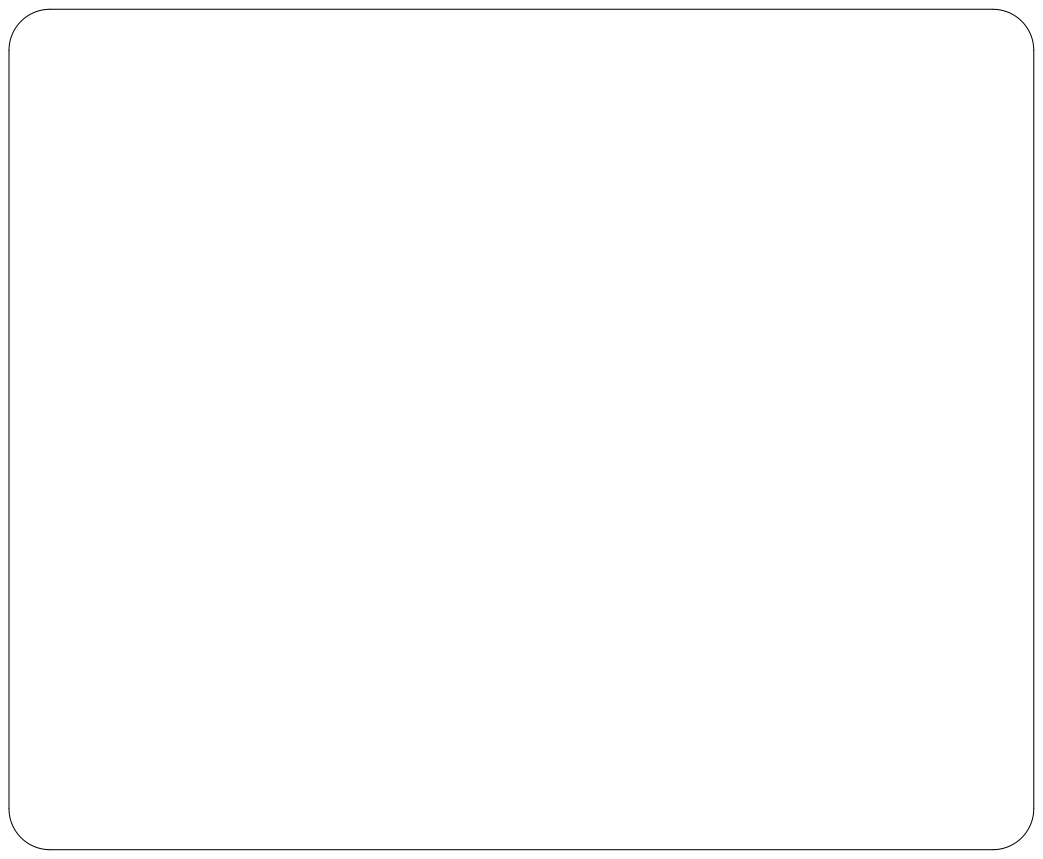
[picture p115: page 1]
