martinanus/salt/hardware/salt_ihm/salt_ihm_pdfs/PCB/Layers/salt_ihm-F_Cu.pdf

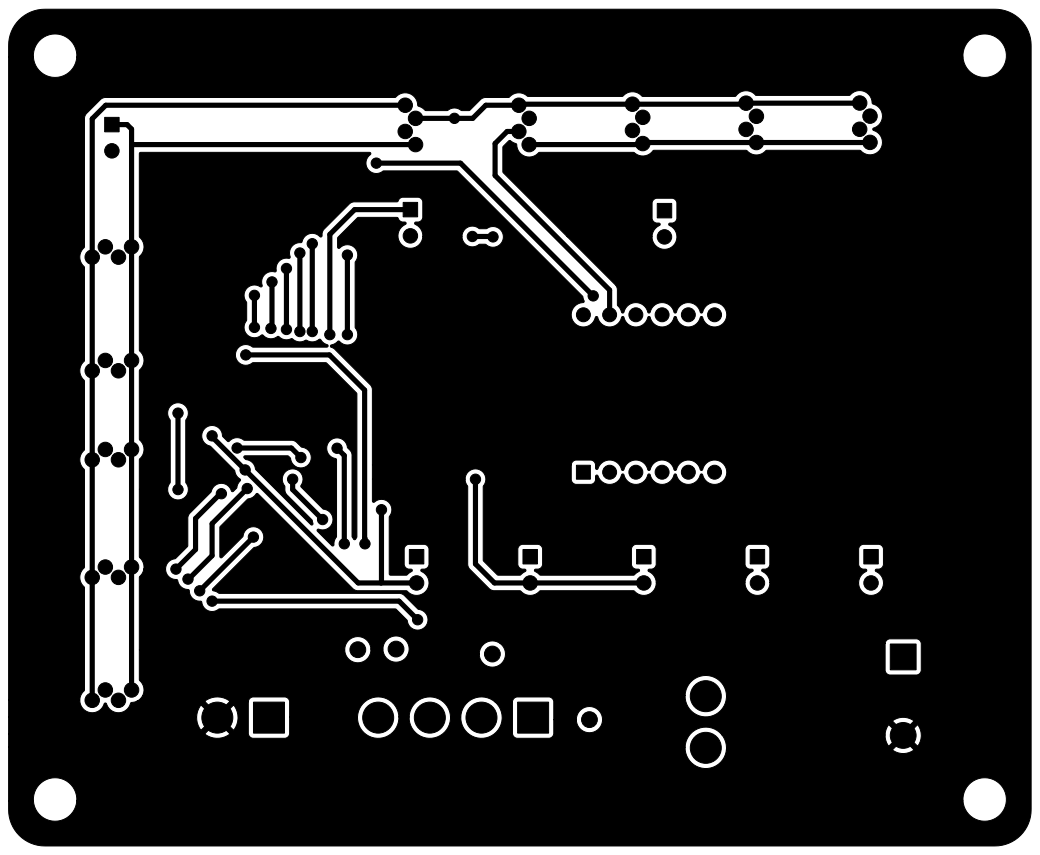
[picture p116: page 1]
