martinanus/salt/hardware/salt_ihm/salt_ihm_pdfs/PCB/Layers/salt_ihm-F_Mask.pdf

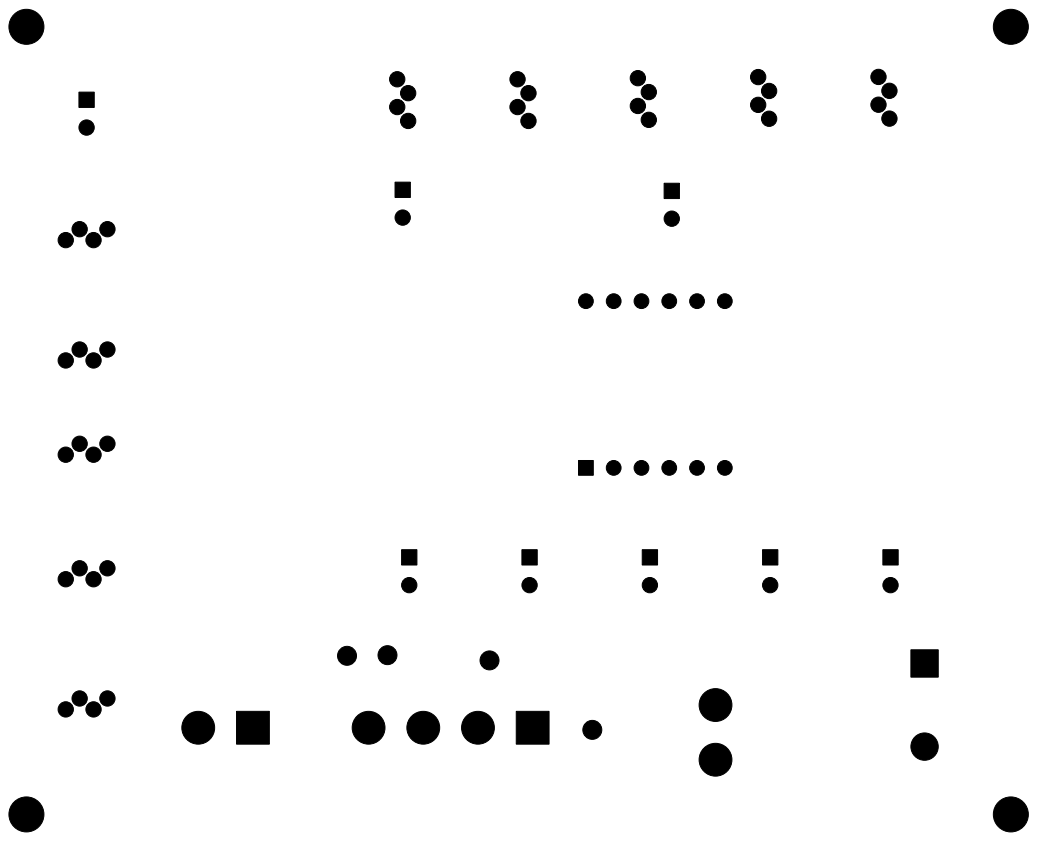
[picture p117: page 1]
