martinanus/salt/hardware/salt_ihm/salt_ihm_pdfs/PCB/Layers/salt_ihm-F_Silkscreen.pdf

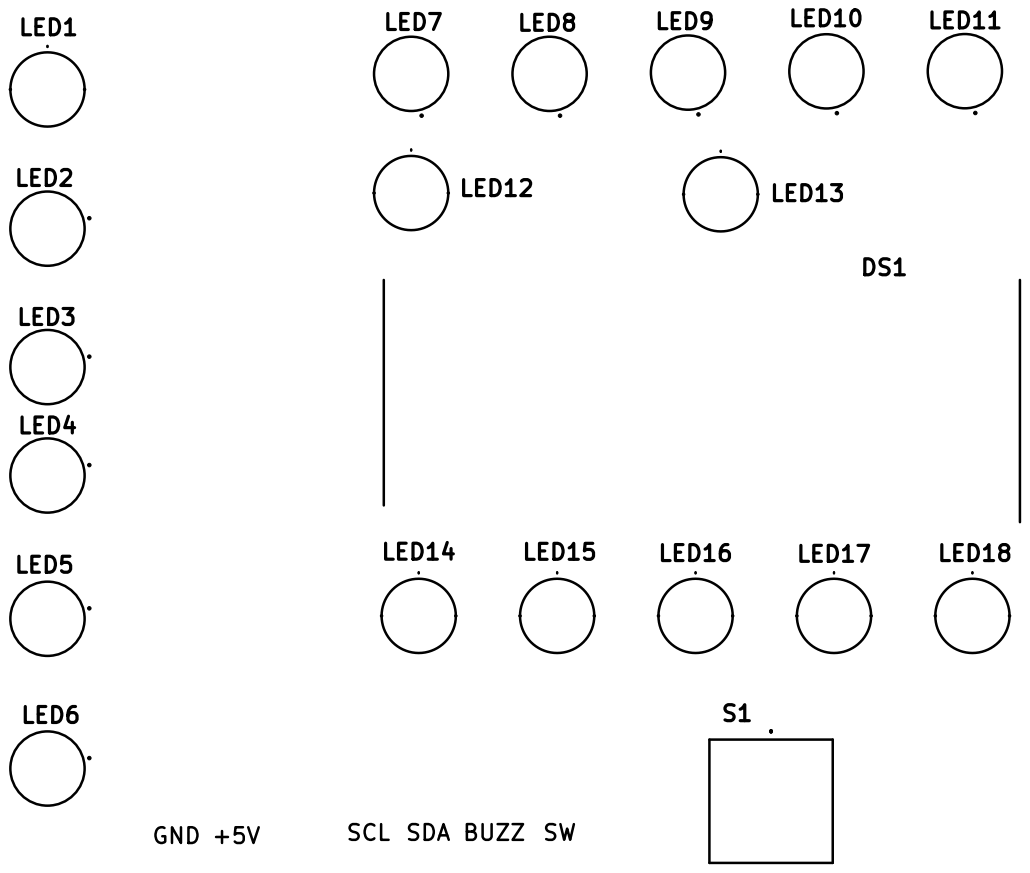
[picture p118: page 1]
