martinanus/salt/hardware/salt_ihm/salt_ihm_pdfs/PCB/Layers/salt_ihm-User_Comments.pdf

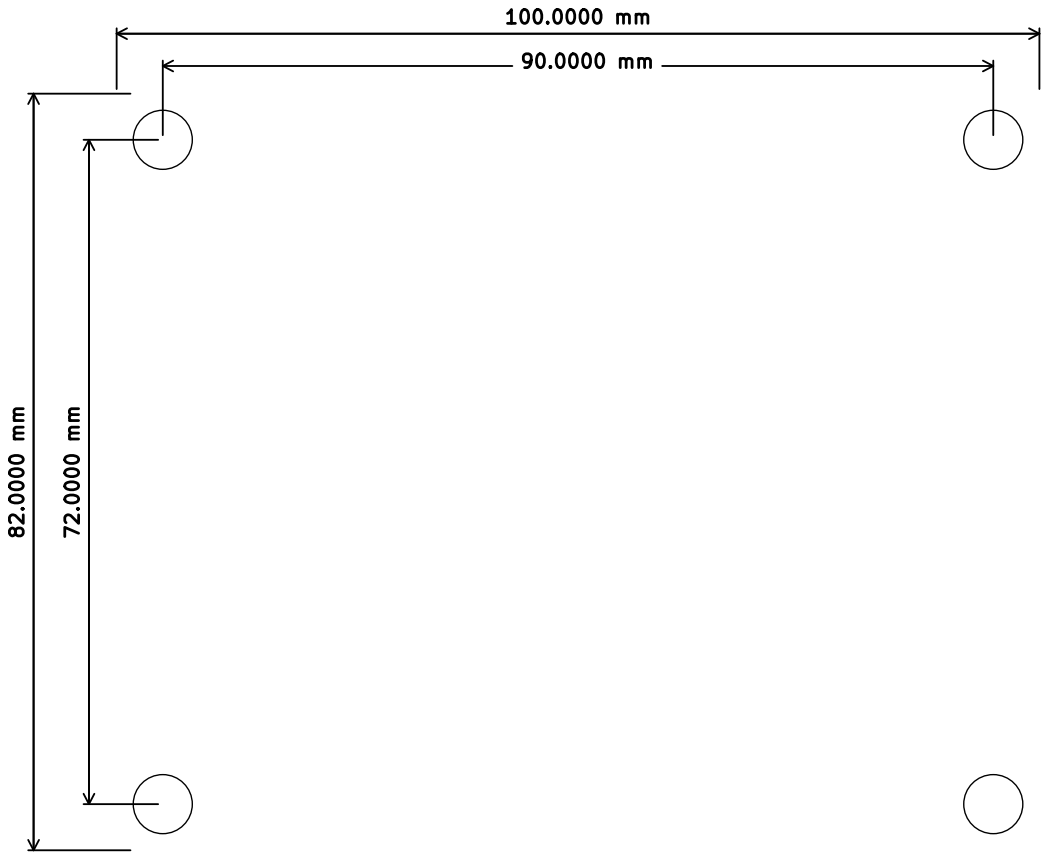
[picture p119: page 1]
