martinanus/salt/firmware/Nucleo144/SALT_freeRTOS/Core/Inc/gps.h

/*
 * gps.h
 *
 *  Created on: May 14, 2024
 *      Author: manus
 */

#ifndef SRC_GPS_H_
#define SRC_GPS_H_

// #include "stm32f4xx_hal.h"

#define MAX_STRING_LENGTH 100
#define MAX_FIELD_LENGTH 20
#define LOG_HEADER_LENGTH 5
#define CHECKSUM_LENGTH 2

#define LATITUDE_DEGREES_LENGTH 2
#define LATITUDE_MINUTES_LENGTH 8
#define LATITUDE_SECONDS_LENGTH 0
#define LONGITUDE_DEGREES_LENGTH 3
#define LONGITUDE_MINUTES_LENGTH 8
#define LONGITUDE_SECONDS_LENGTH 0

#define DAYS_LENGTH 2
#define MONTHS_LENGTH 2
#define YEARS_LENGTH 2
#define UTC_HOURS_LENGTH 2
#define UTC_MINUTES_LENGTH 2
#define UTC_SECOND_LENGTH 5

#define RADIUS_EARTH 6371 // km
#define M_PI 3.14159265358979323846

typedef struct
{
	int degrees;
	int minutes;
	int seconds;
	char direction;
} dms_coordinates_t;

typedef struct
{
	double latitude;
	double longitude;
} dd_location_d;

typedef struct
{
	int year;
	int month;
	int day;
	int hours;
	int minutes;
	float seconds;
} datetime_t;

struct GPRMC
{
	char log_header[LOG_HEADER_LENGTH + 1]; //  1- $ + GPRMC
	datetime_t datetime;					//  2- hhmmss.ss | 10- ddmmmyy
	char status;							//  3- A=valid | V=invalid
	dms_coordinates_t latitude;				//  4- latitude DDmm.mm | 5- N=north | S=south
	dms_coordinates_t longitude;			//  6- longitud DDdmm.mm | 7- E=east | W=west
	float speed;							//  8- SoG, knots
	// track make good                          9
	// mag var                                 11
	// mag var dir                             12
	char checksum[CHECKSUM_LENGTH + 1]; // 13- Mode + *xx + CR-LF
};

void parse_GPRMC(const char *line, struct GPRMC *data);
void print_GPRMC(struct GPRMC *data);
// void transmit_GPRMC(UART_HandleTypeDef *huart, struct GPRMC *data);
double dms_to_decimal(dms_coordinates_t coordinate);
dd_location_d convert_dms_to_decimal(dms_coordinates_t coordinate1, dms_coordinates_t coordinate2);
double haversine_distance(dd_location_d point1, dd_location_d point2);

#endif /* SRC_GPS_H_ */
